KaiPereira/build-a-devboard/journal/Pasted image 20250828214635.png

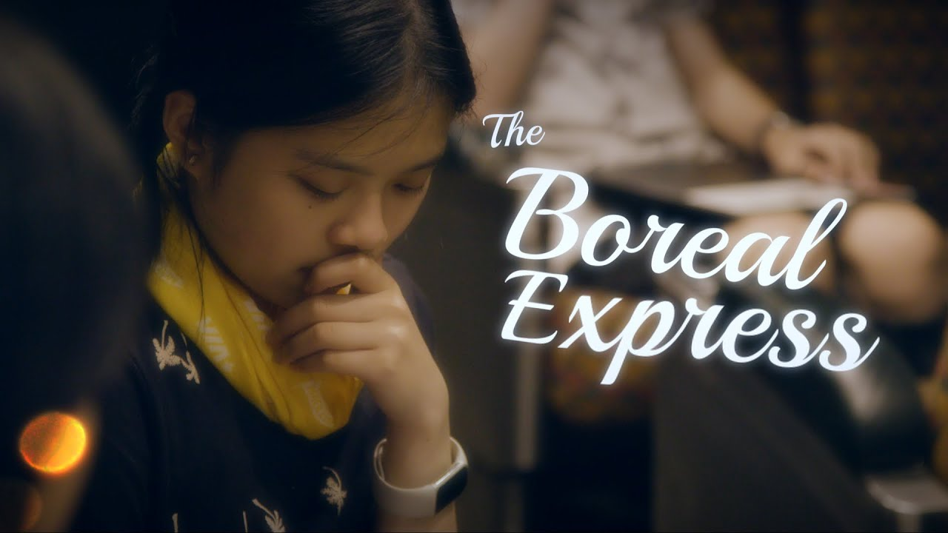
journal/Pasted image 20250828214635.png
