KaiPereira/build-a-devboard/journal/Pasted image 20250828221741.png

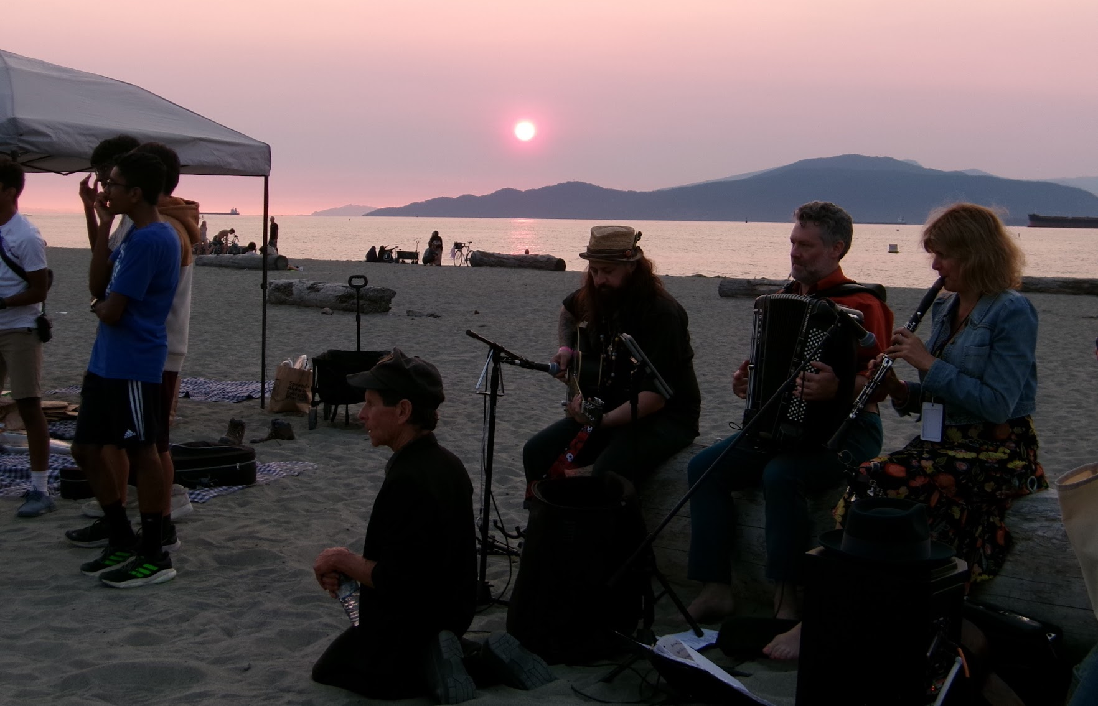
journal/Pasted image 20250828221741.png
