KaiPereira/build-a-devboard/journal/Pasted image 20250828224618.png

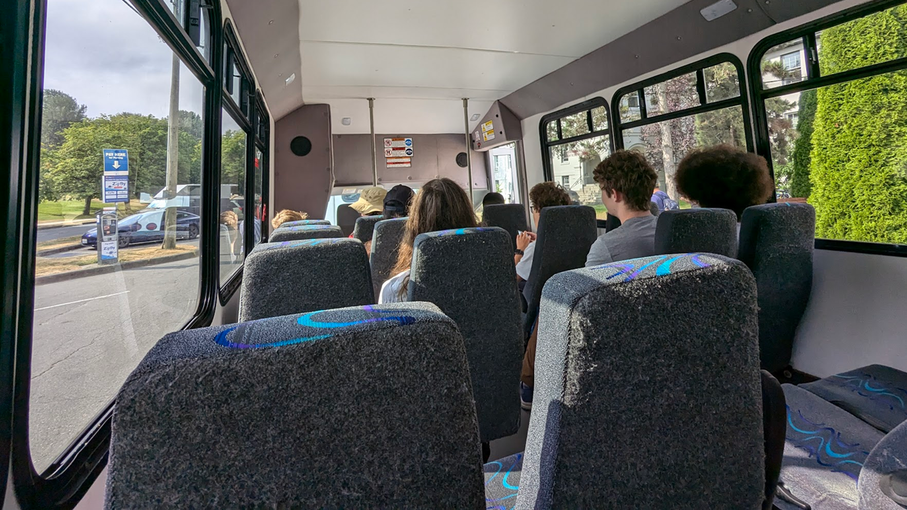
journal/Pasted image 20250828224618.png
