KaiPereira/build-a-devboard/journal/Pasted image 20250828224701.png

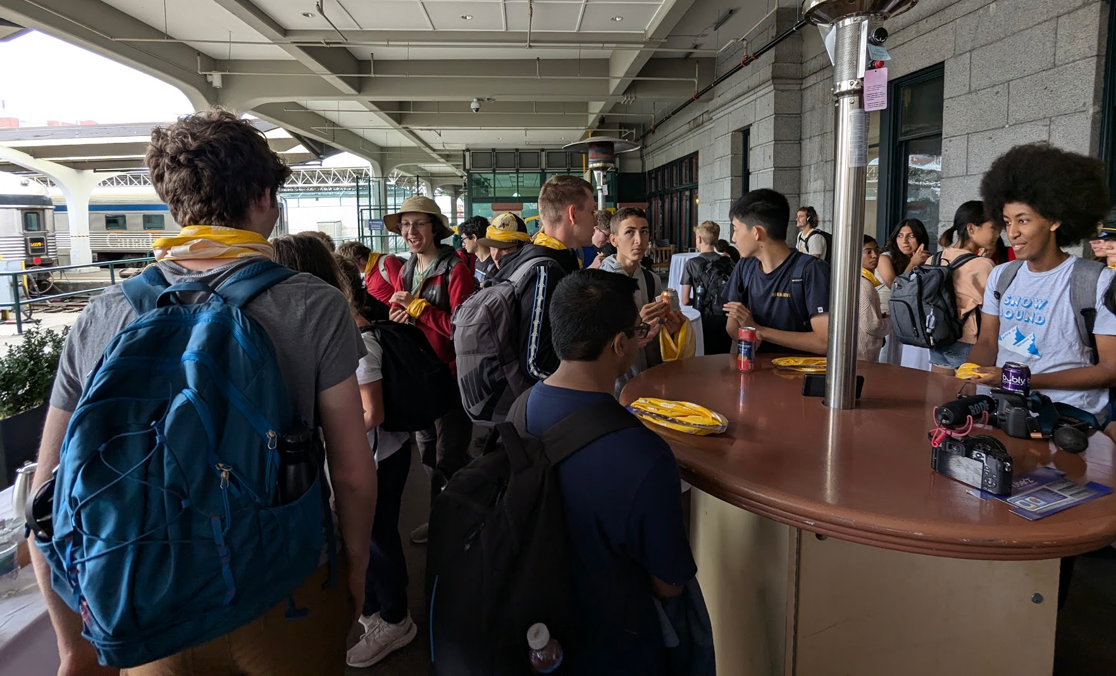
journal/Pasted image 20250828224701.png
