KaiPereira/build-a-devboard/journal/Pasted image 20250828225130.png

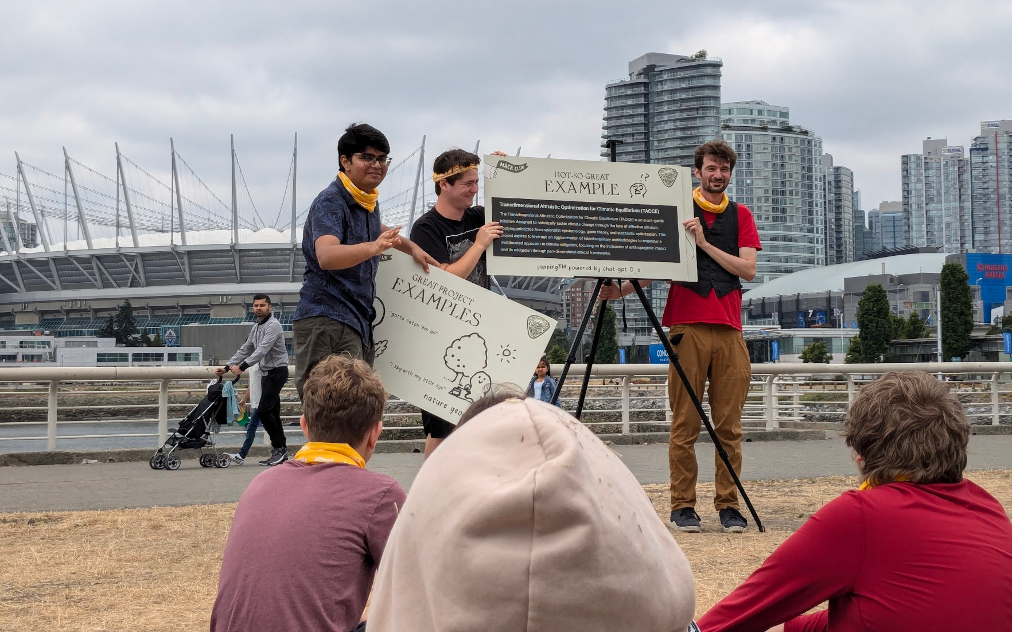
journal/Pasted image 20250828225130.png
