KaiPereira/build-a-devboard/journal/Pasted image 20250828225333.png

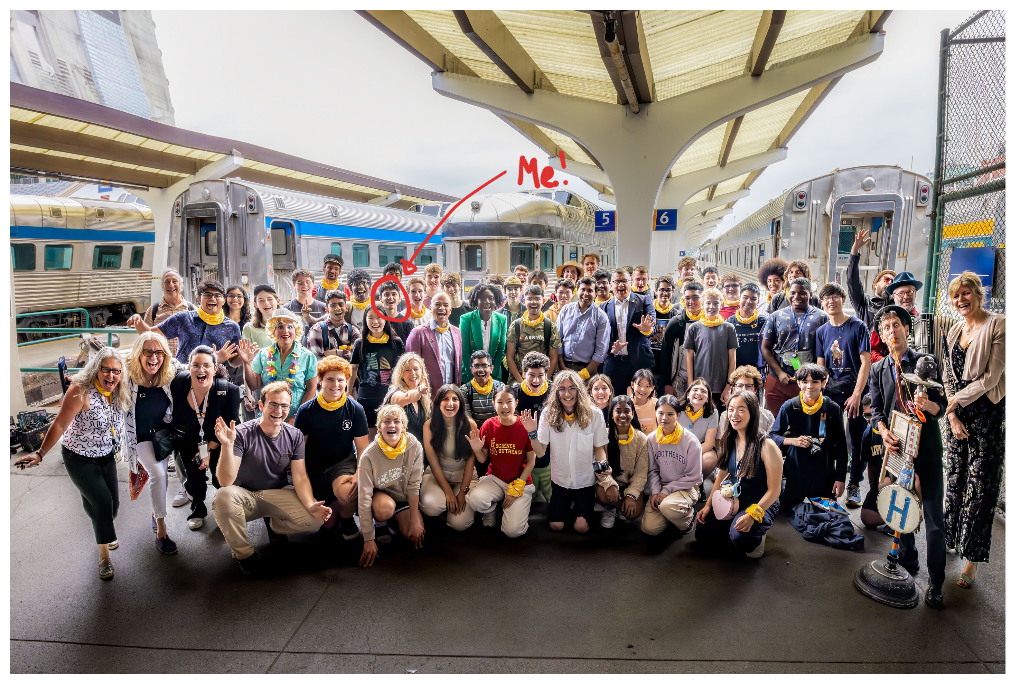
journal/Pasted image 20250828225333.png
