KaiPereira/build-a-devboard/journal/Pasted image 20250828225424.png

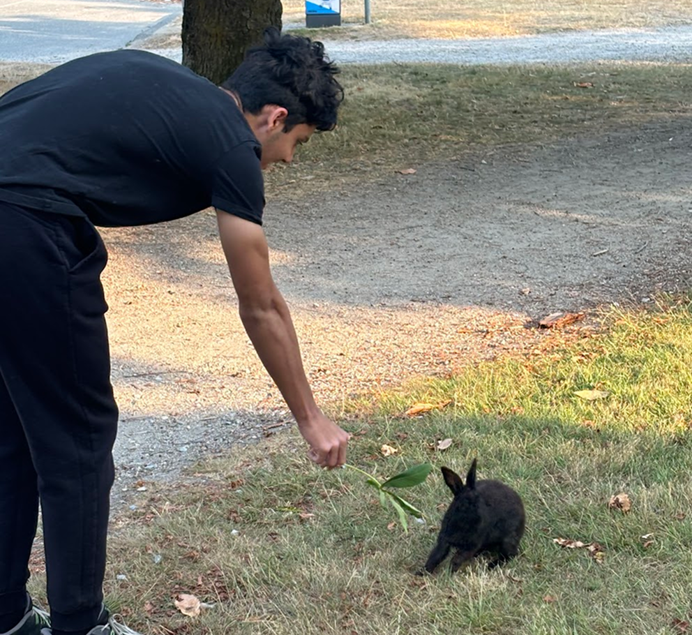
journal/Pasted image 20250828225424.png
