KaiPereira/build-a-devboard/journal/Pasted image 20250828230733.png

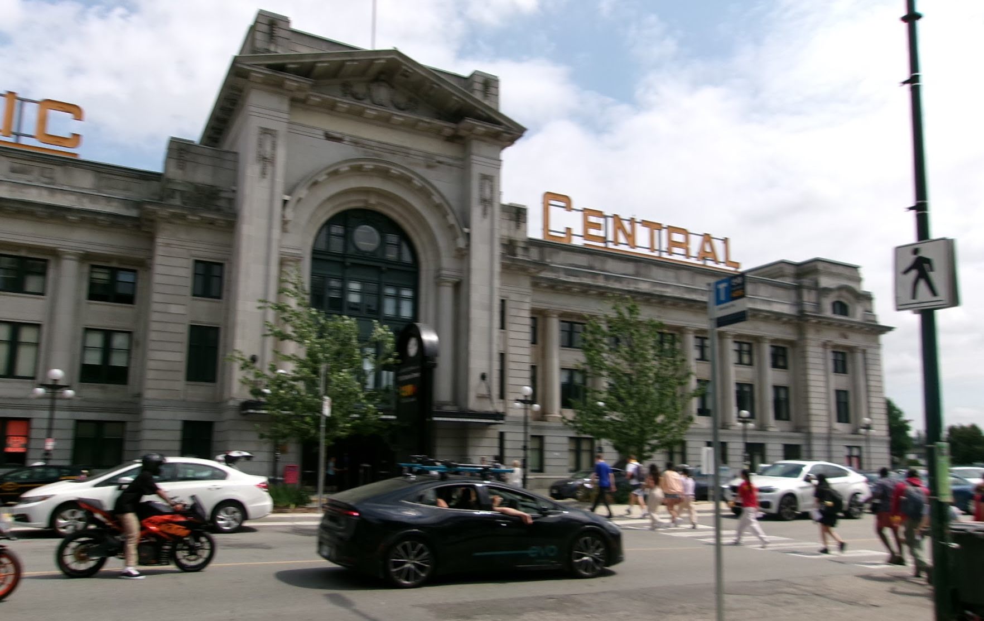
journal/Pasted image 20250828230733.png
