KaiPereira/build-a-devboard/journal/Pasted image 20250828233427.png

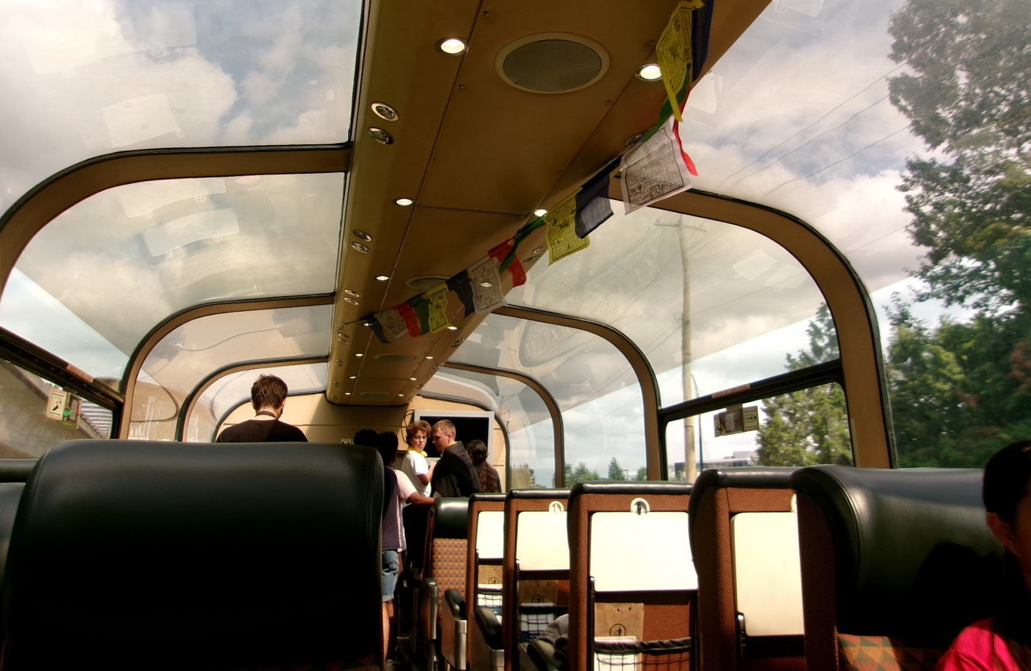
journal/Pasted image 20250828233427.png
