KaiPereira/build-a-devboard/journal/Pasted image 20250828234556.png

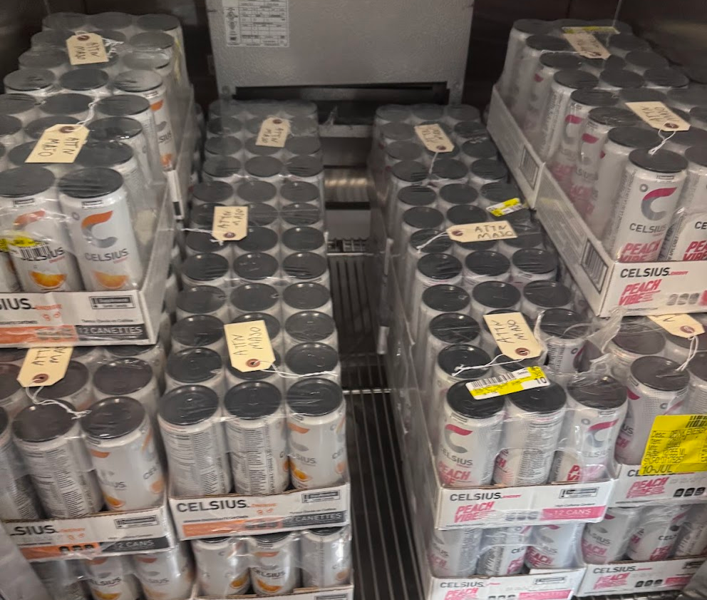
journal/Pasted image 20250828234556.png
