KaiPereira/build-a-devboard/journal/Pasted image 20250828234612.png

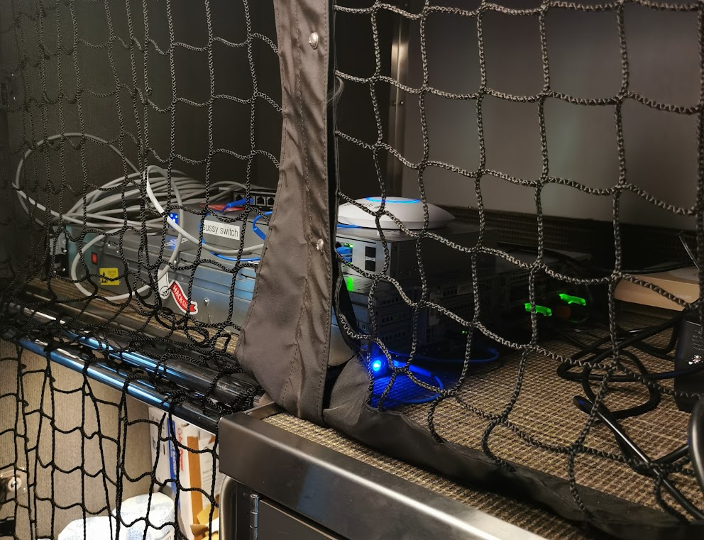
journal/Pasted image 20250828234612.png
