KaiPereira/build-a-devboard/journal/Pasted image 20250828234858.png

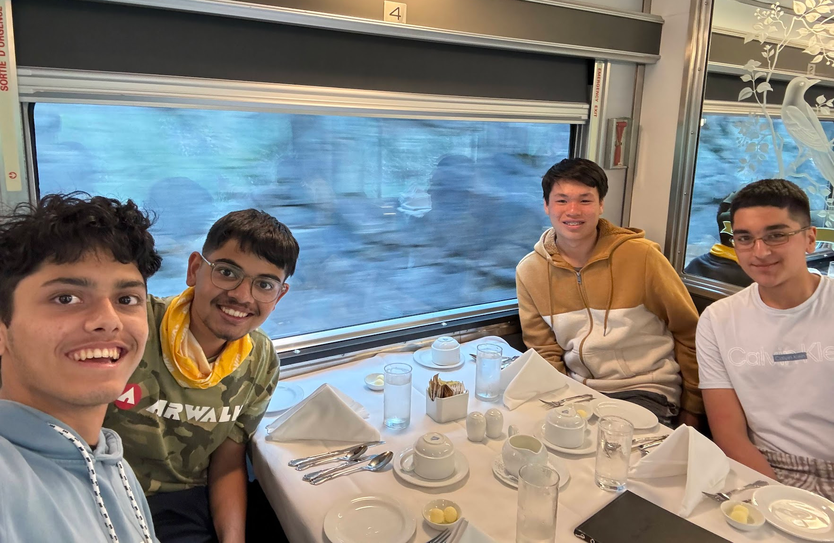
journal/Pasted image 20250828234858.png
