KaiPereira/build-a-devboard/journal/Pasted image 20250829002450.png

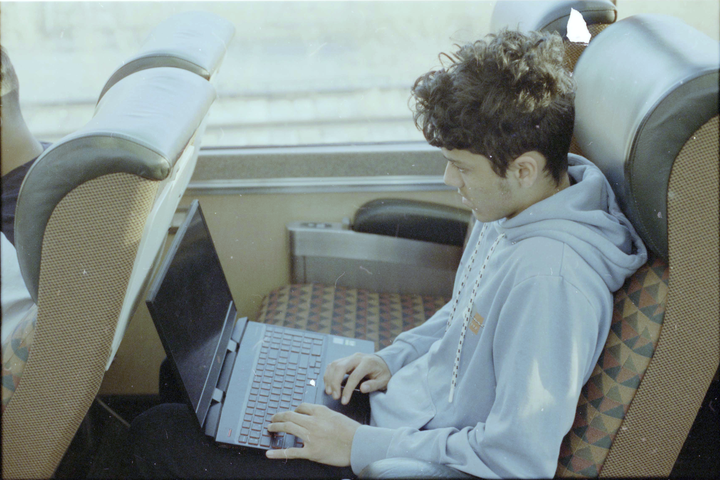
journal/Pasted image 20250829002450.png
