KaiPereira/build-a-devboard/journal/Pasted image 20250829003156.png

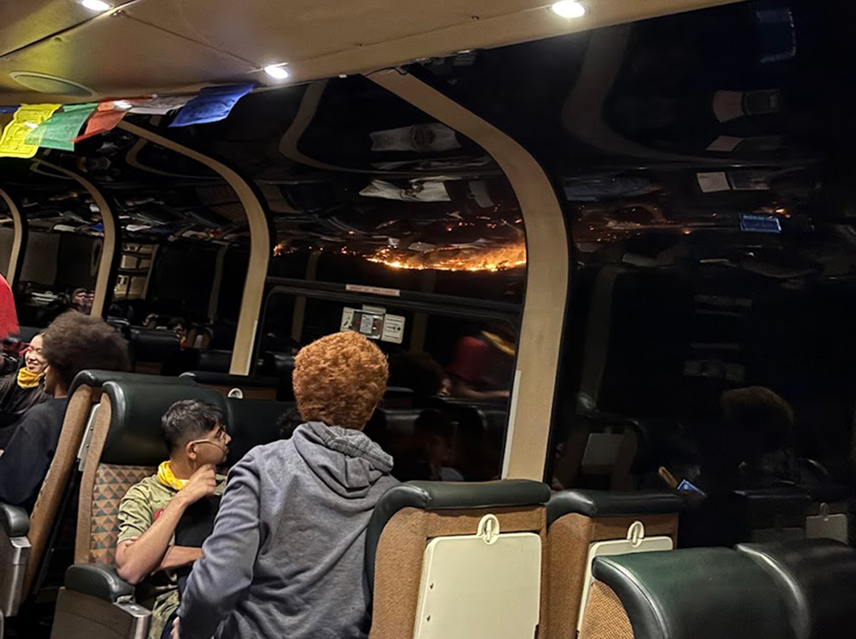
journal/Pasted image 20250829003156.png
