KaiPereira/build-a-devboard/journal/Pasted image 20250829004820.png

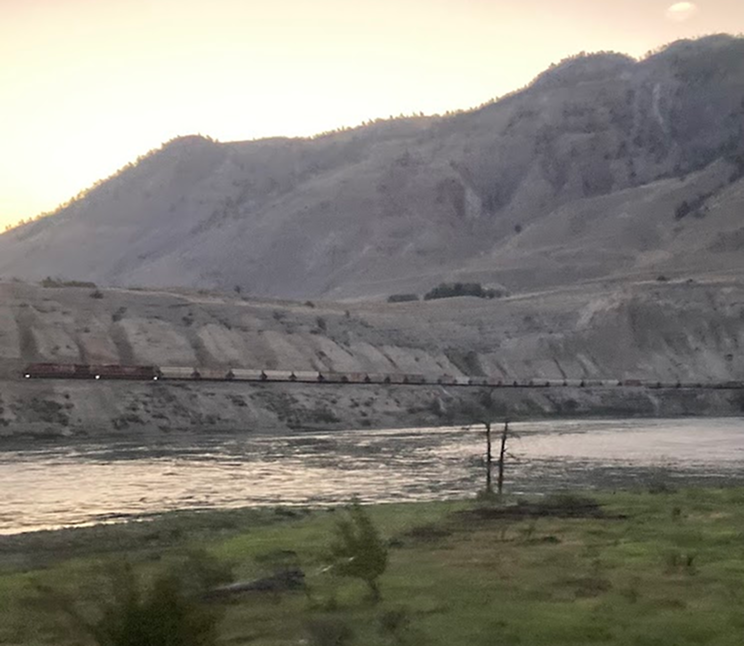
journal/Pasted image 20250829004820.png
