KaiPereira/build-a-devboard/journal/Pasted image 20250829005805.png

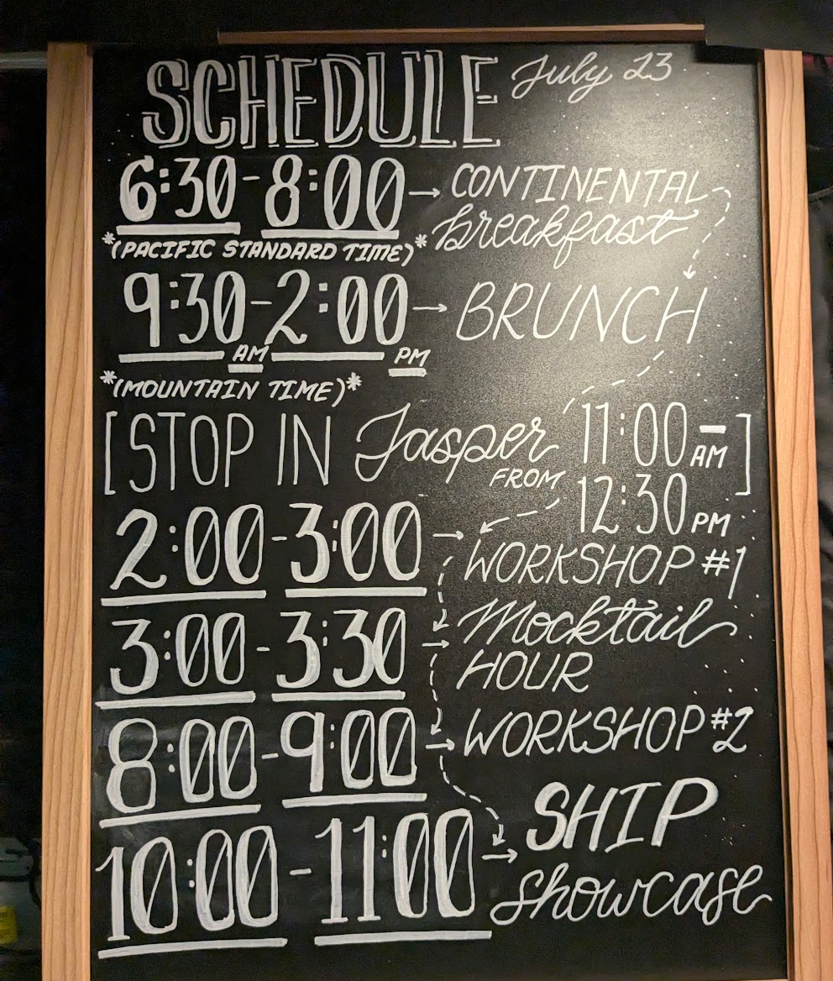
journal/Pasted image 20250829005805.png
