KaiPereira/build-a-devboard/journal/Pasted image 20250829161614.png

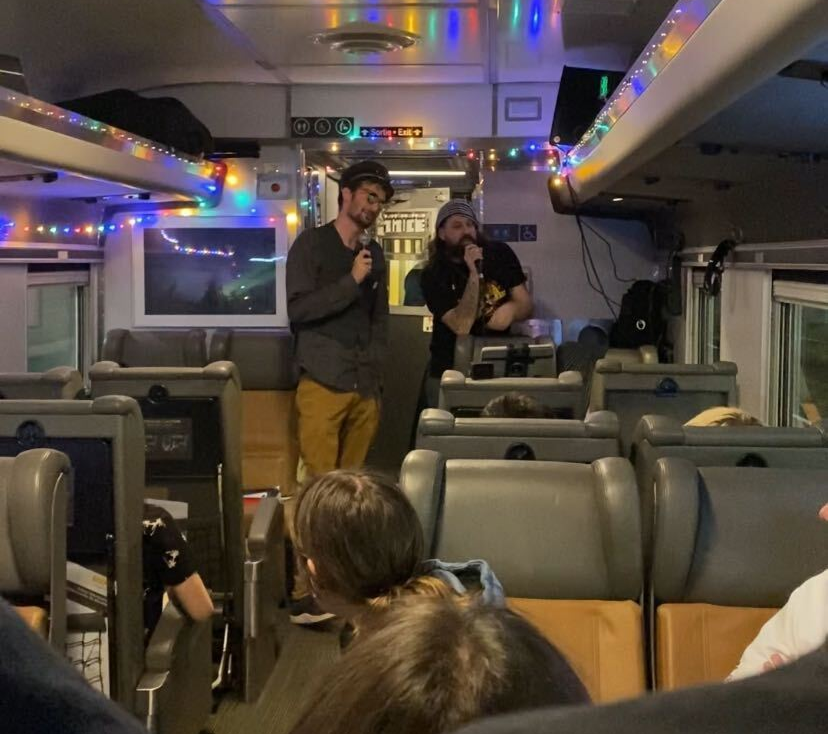
journal/Pasted image 20250829161614.png
