KaiPereira/build-a-devboard/journal/Pasted image 20250829162045.png

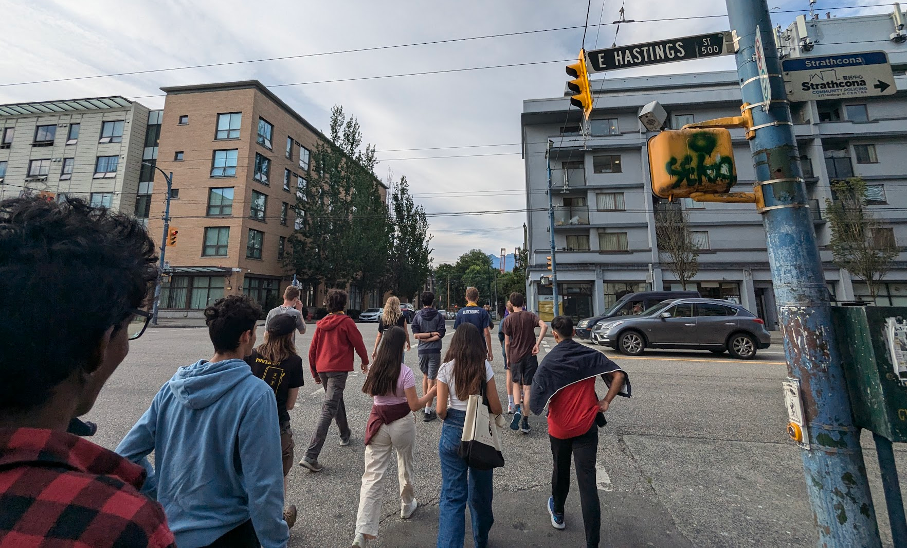
journal/Pasted image 20250829162045.png
