KaiPereira/build-a-devboard/journal/Pasted image 20250829164850.png

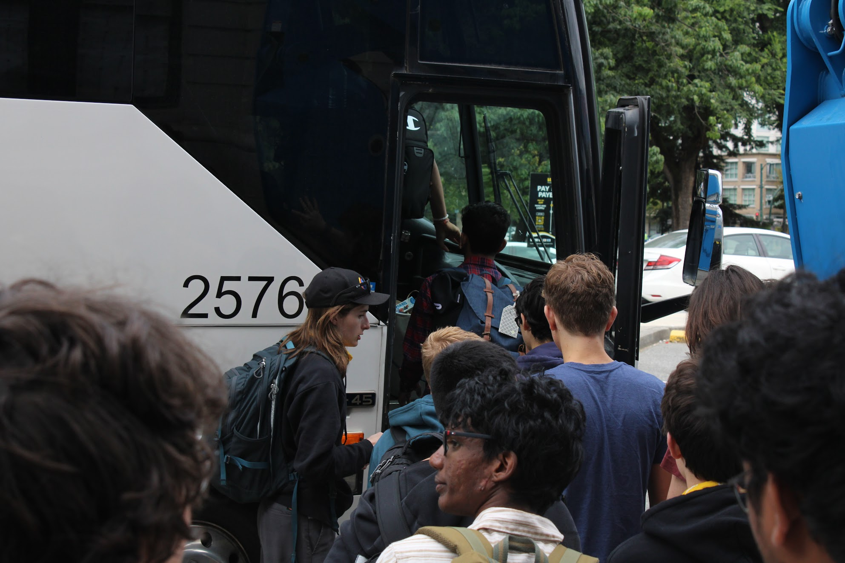
journal/Pasted image 20250829164850.png
