KaiPereira/build-a-devboard/journal/Pasted image 20250829165105.png

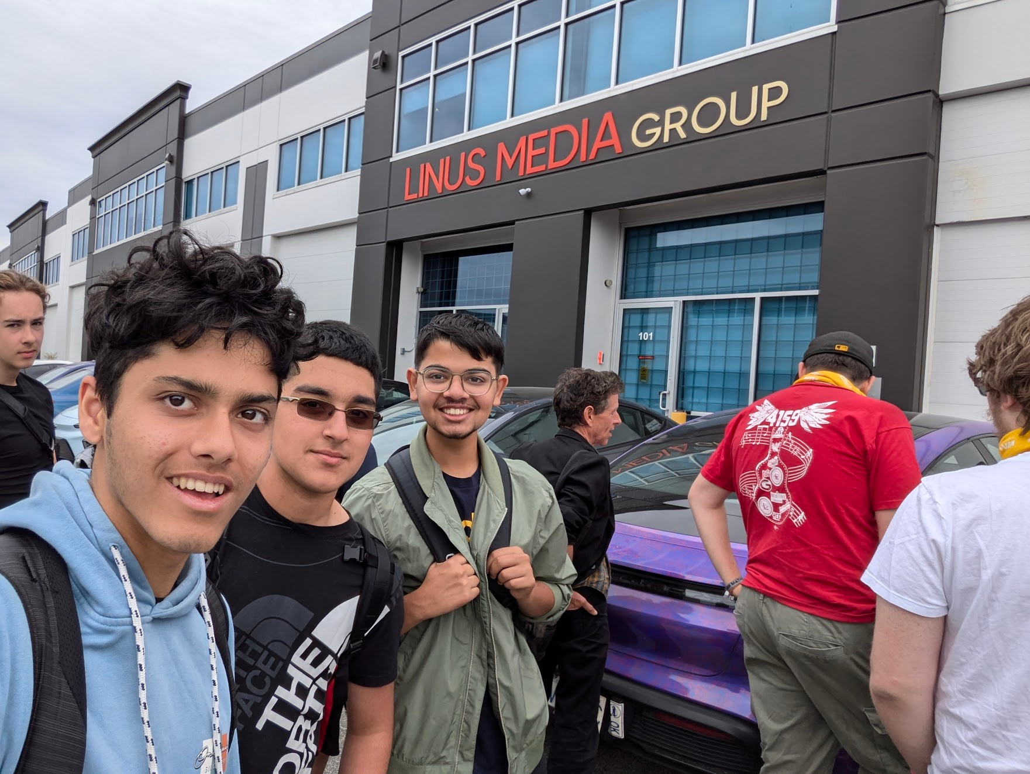
journal/Pasted image 20250829165105.png
