KaiPereira/build-a-devboard/journal/Pasted image 20250829165130.png

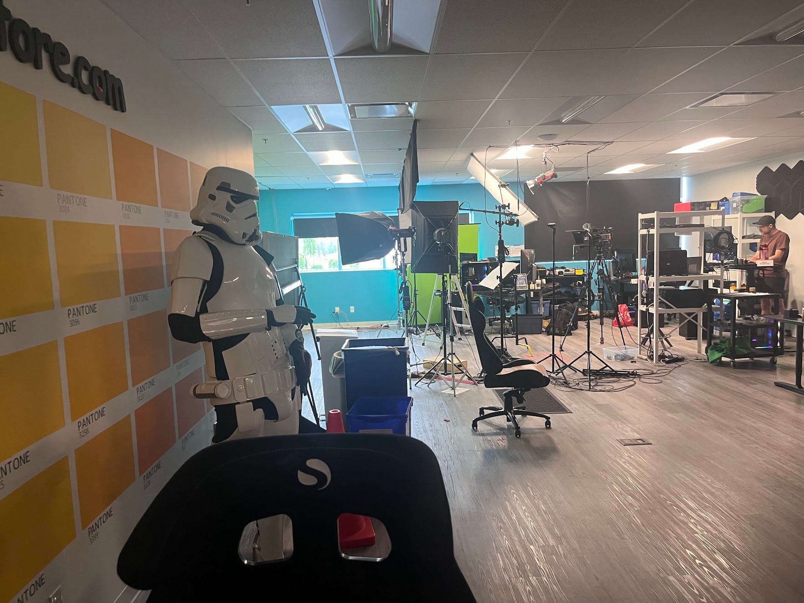
journal/Pasted image 20250829165130.png
