KaiPereira/build-a-devboard/journal/Pasted image 20250829165152.png

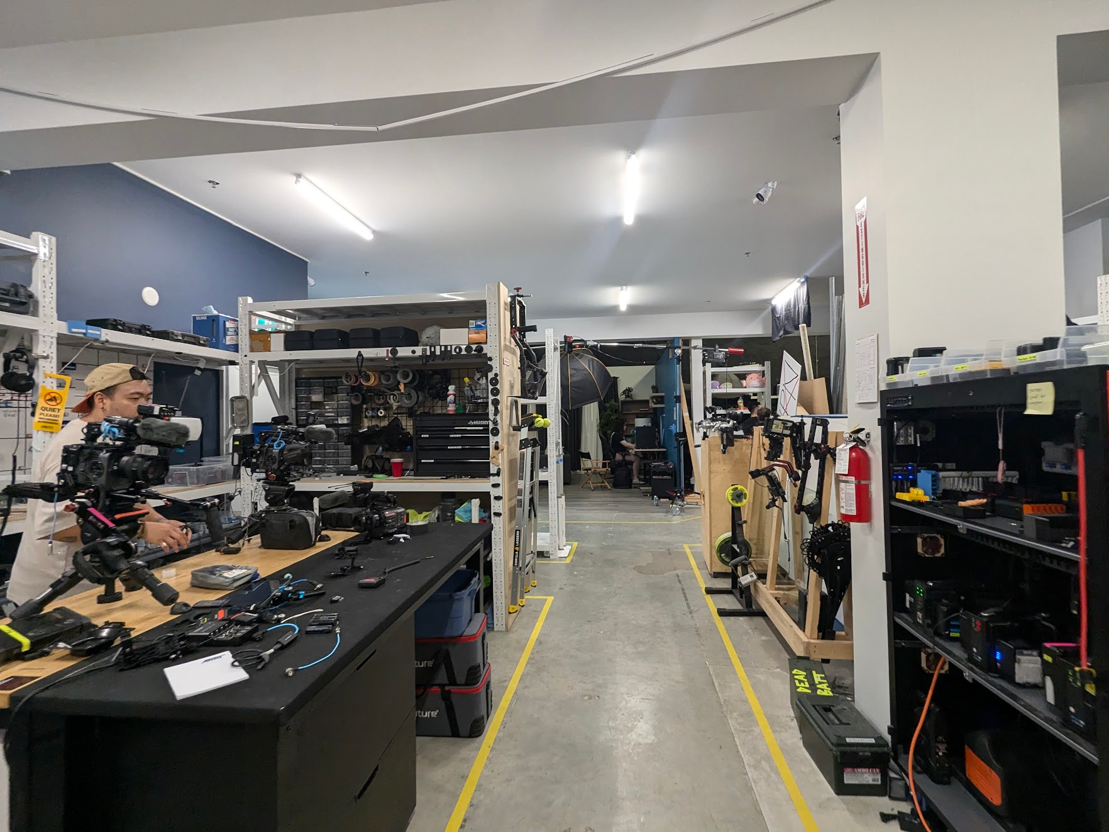
journal/Pasted image 20250829165152.png
