KaiPereira/build-a-devboard/journal/Pasted image 20250829165215.png

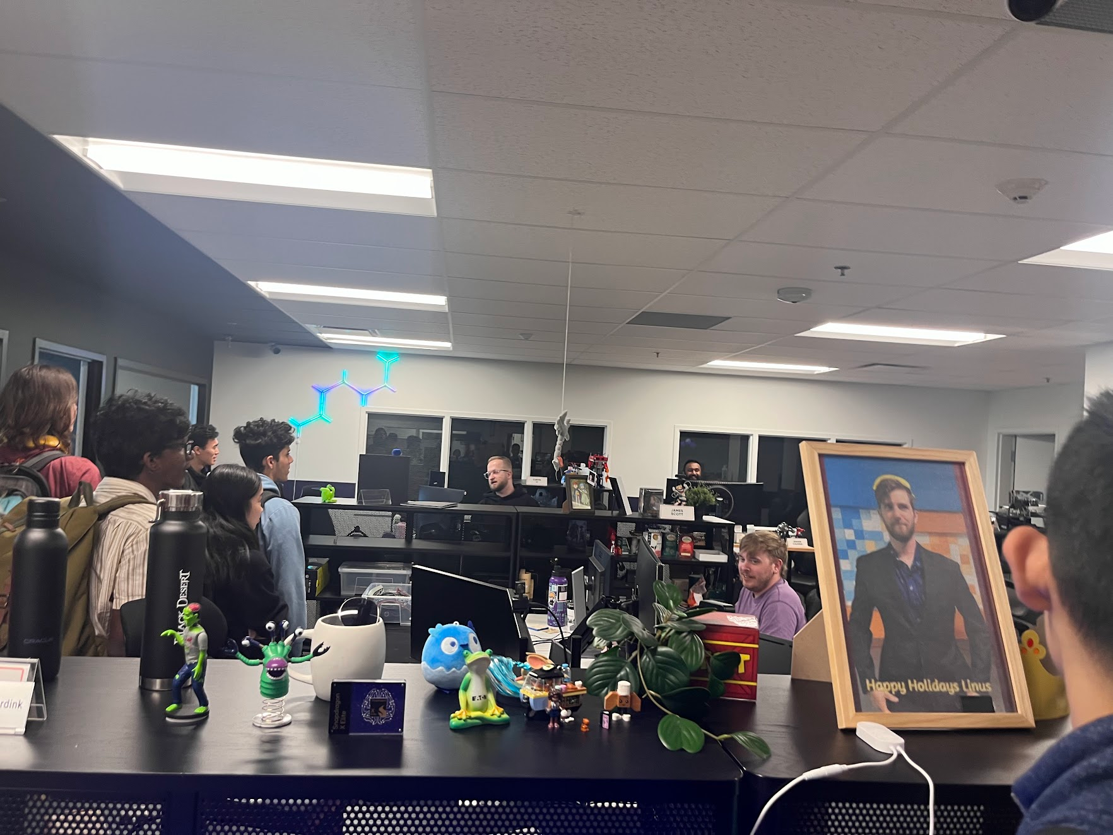
journal/Pasted image 20250829165215.png
