KaiPereira/build-a-devboard/journal/Pasted image 20250829165408.png

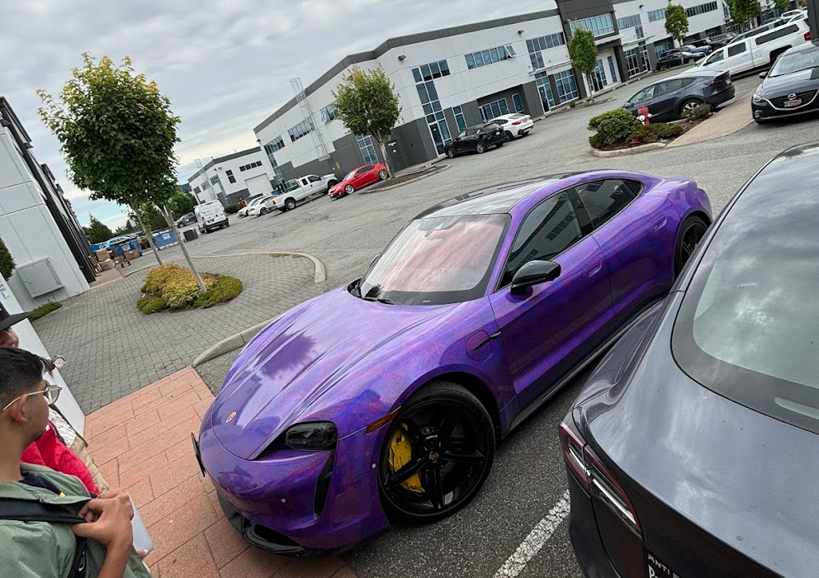
journal/Pasted image 20250829165408.png
