KaiPereira/build-a-devboard/journal/Pasted image 20250829182641.png

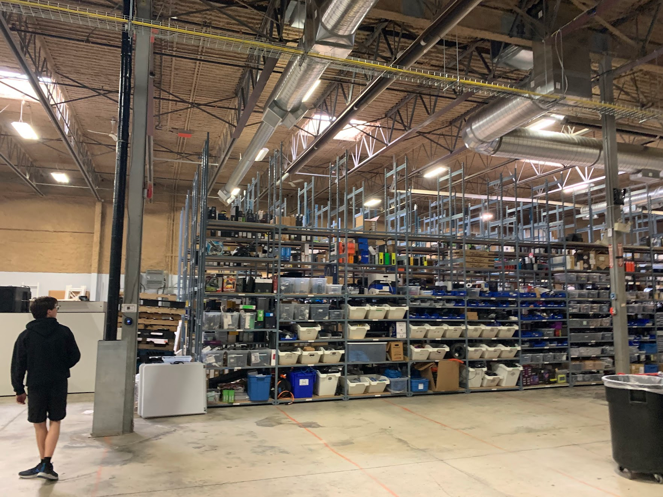
journal/Pasted image 20250829182641.png
