KaiPereira/build-a-devboard/journal/Pasted image 20250925070807.png

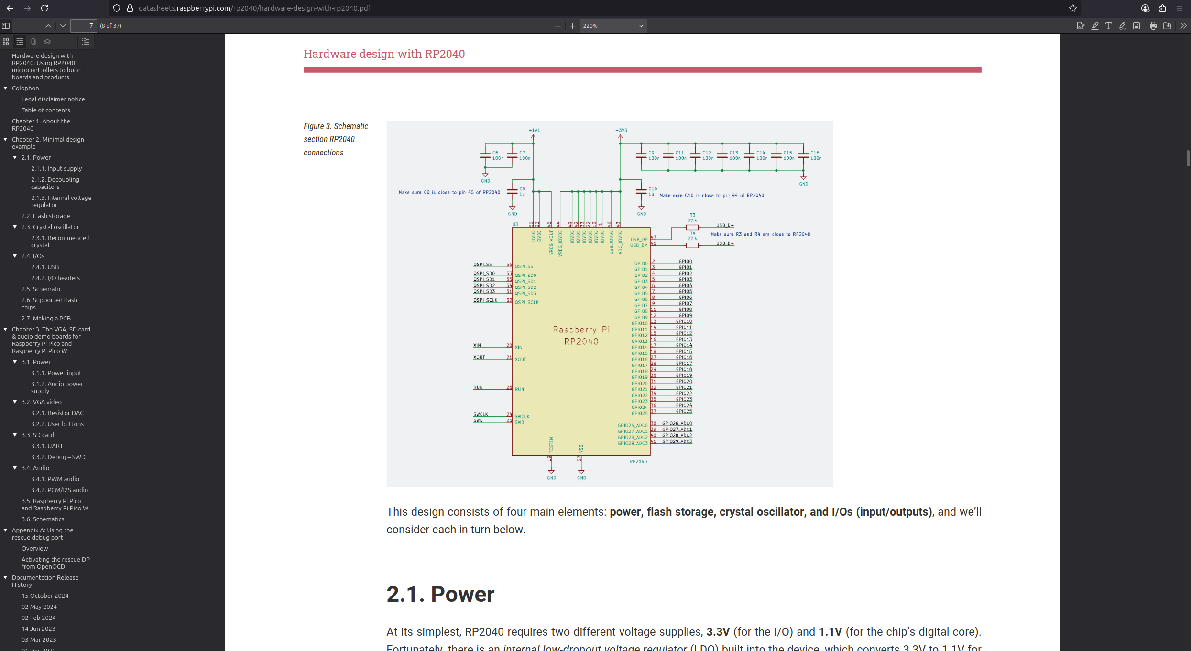
journal/Pasted image 20250925070807.png
