KaiPereira/build-a-devboard/journal/Pasted image 20250925160300.png

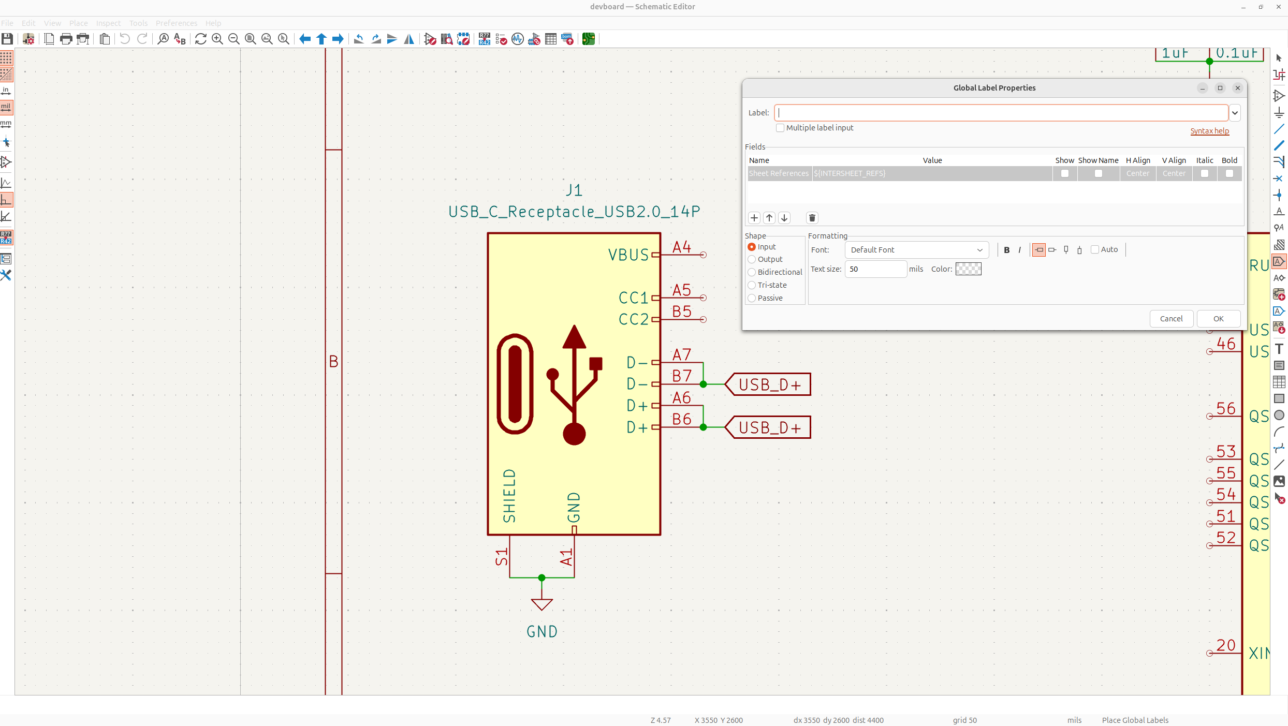
journal/Pasted image 20250925160300.png
