KaiPereira/build-a-devboard/journal/Pasted image 20250925160549.png

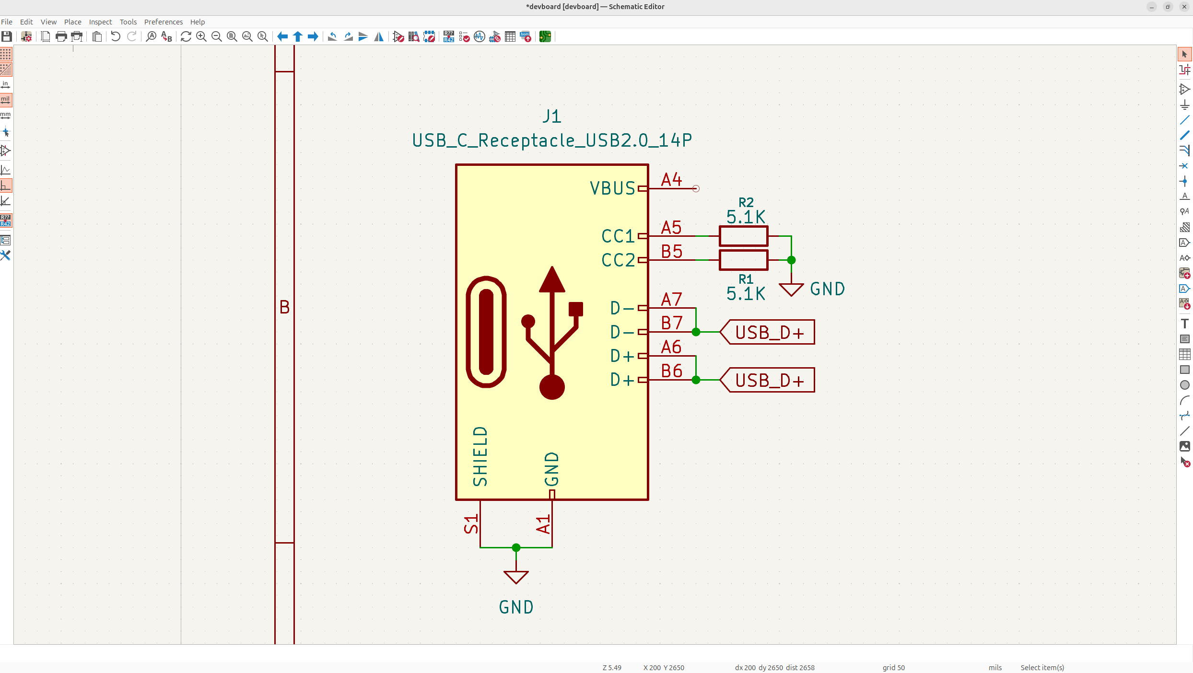
journal/Pasted image 20250925160549.png
