KaiPereira/build-a-devboard/journal/Pasted image 20250925161539.png

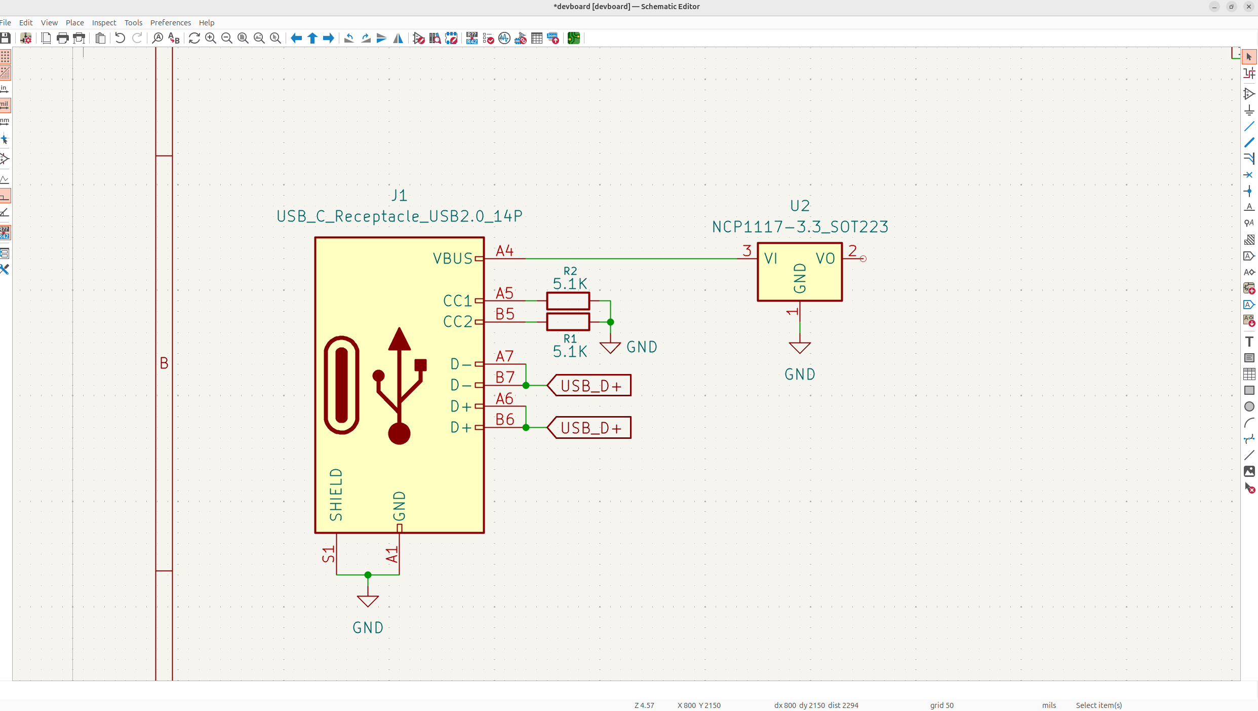
journal/Pasted image 20250925161539.png
