KaiPereira/build-a-devboard/journal/Pasted image 20250925161945.png

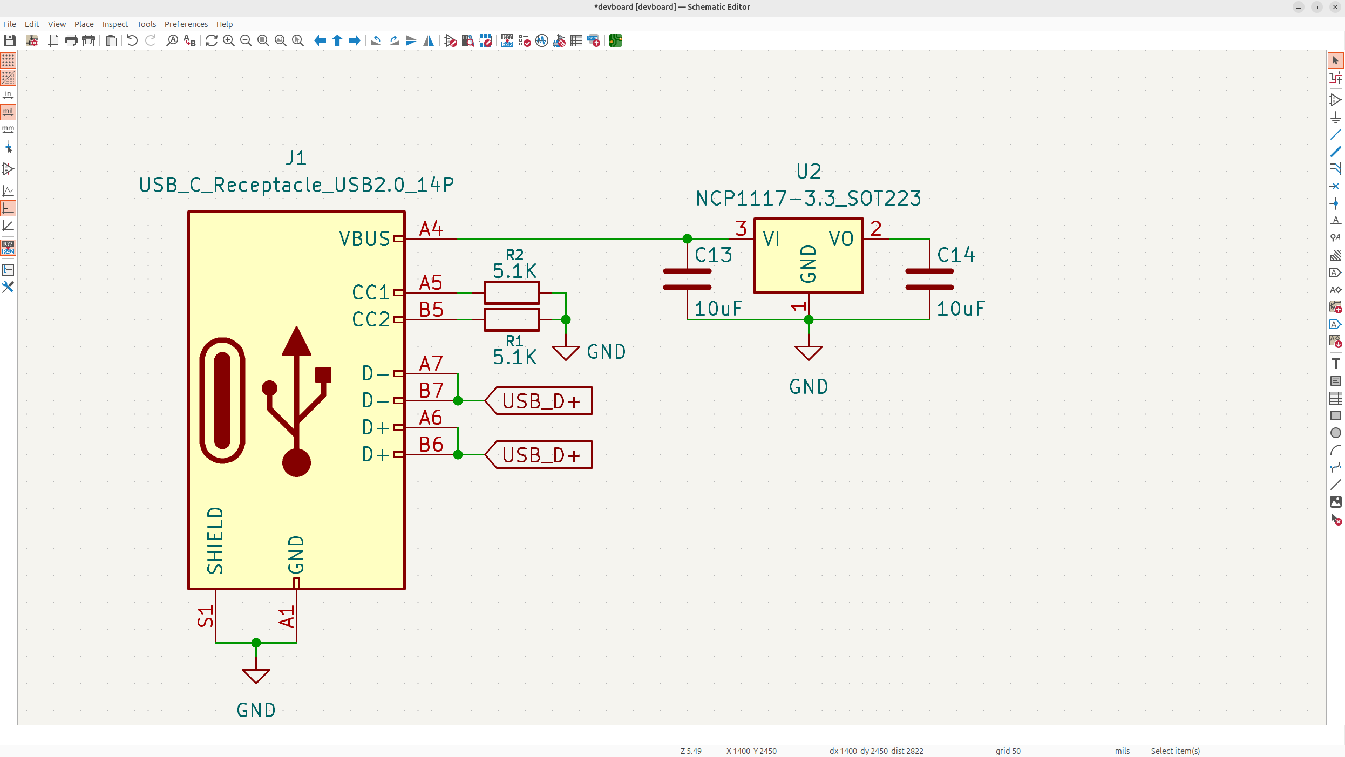
journal/Pasted image 20250925161945.png
