KaiPereira/build-a-devboard/journal/Pasted image 20250925162329.png

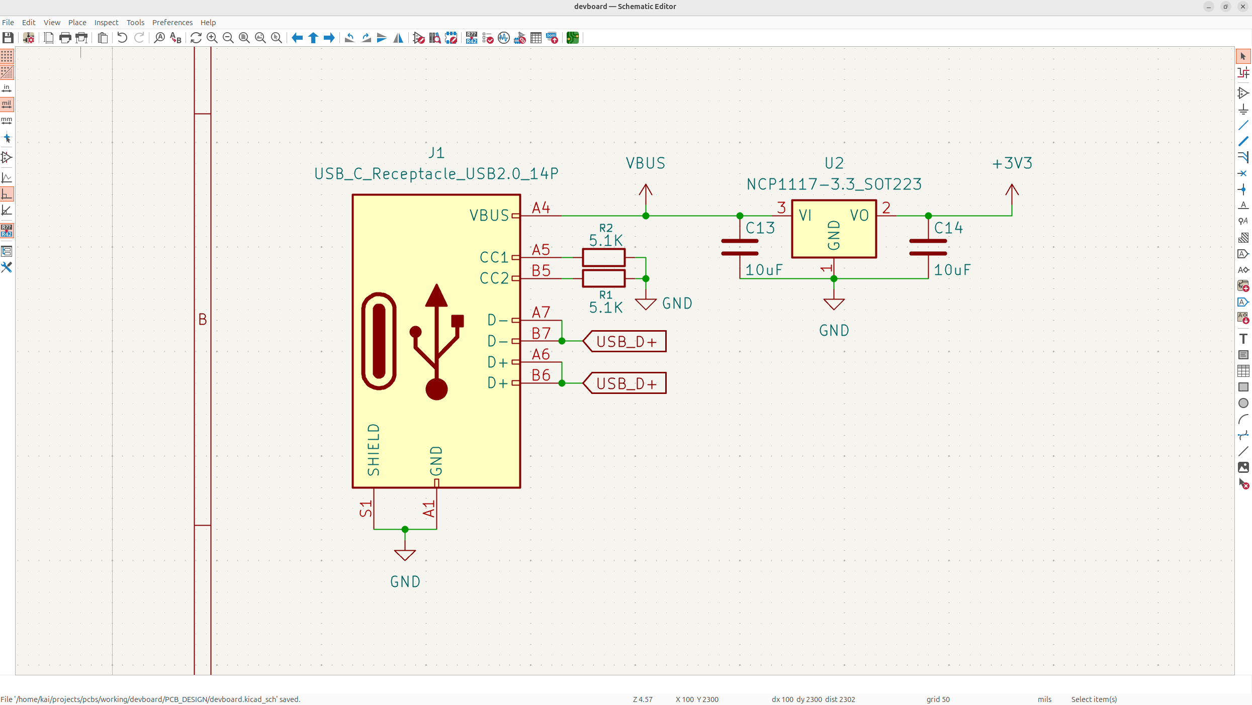
journal/Pasted image 20250925162329.png
