KaiPereira/build-a-devboard/journal/Pasted image 20250927190151.png

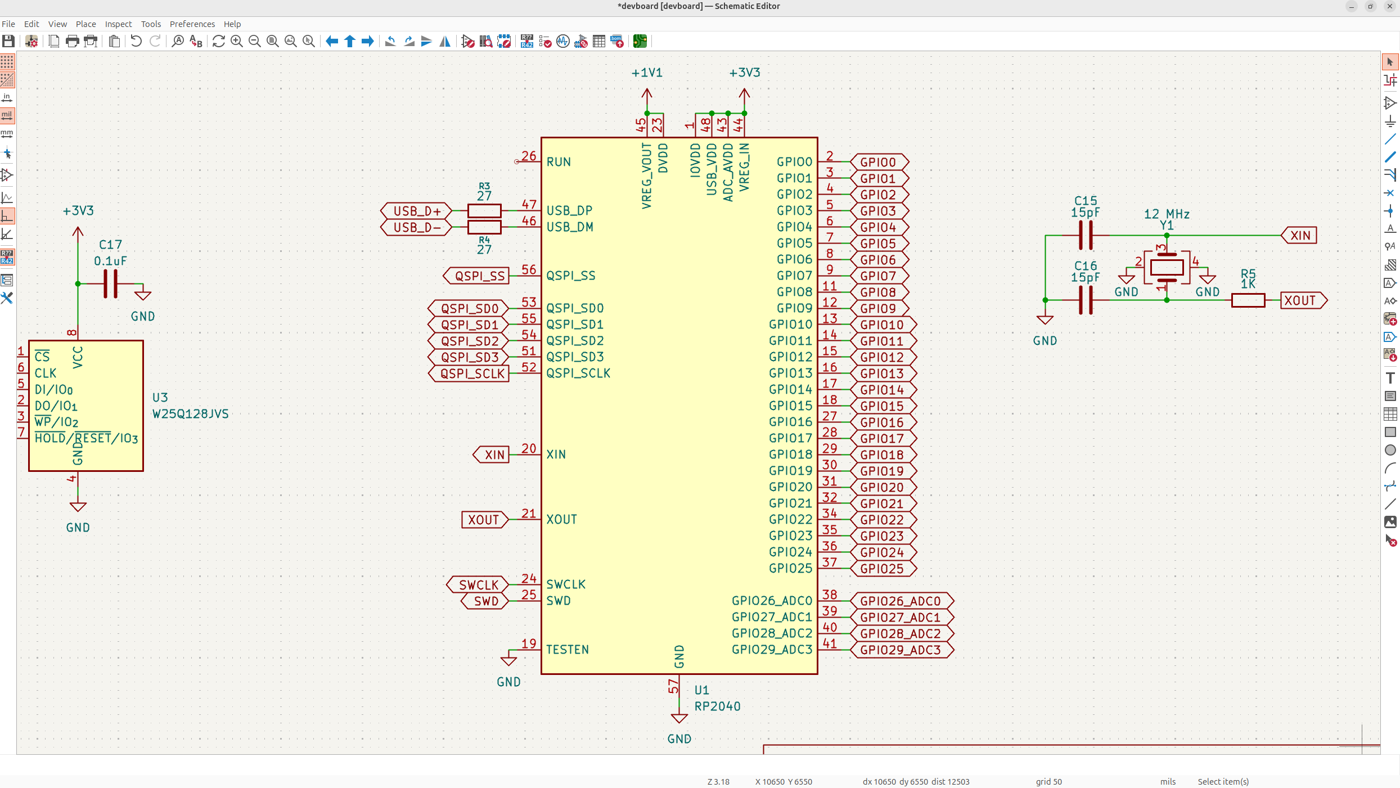
journal/Pasted image 20250927190151.png
