KaiPereira/build-a-devboard/journal/Pasted image 20250927190319.png

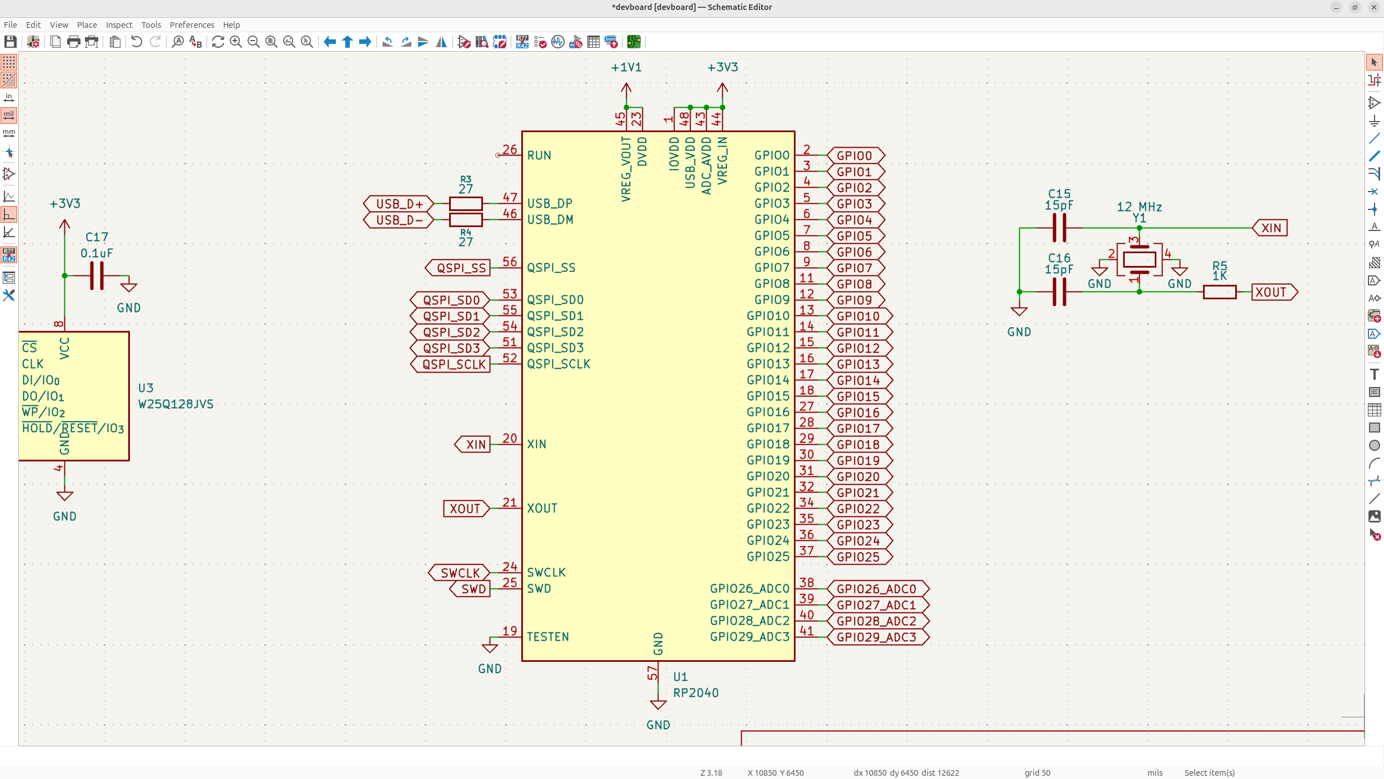
journal/Pasted image 20250927190319.png
