KaiPereira/build-a-devboard/journal/Pasted image 20250928011307.png

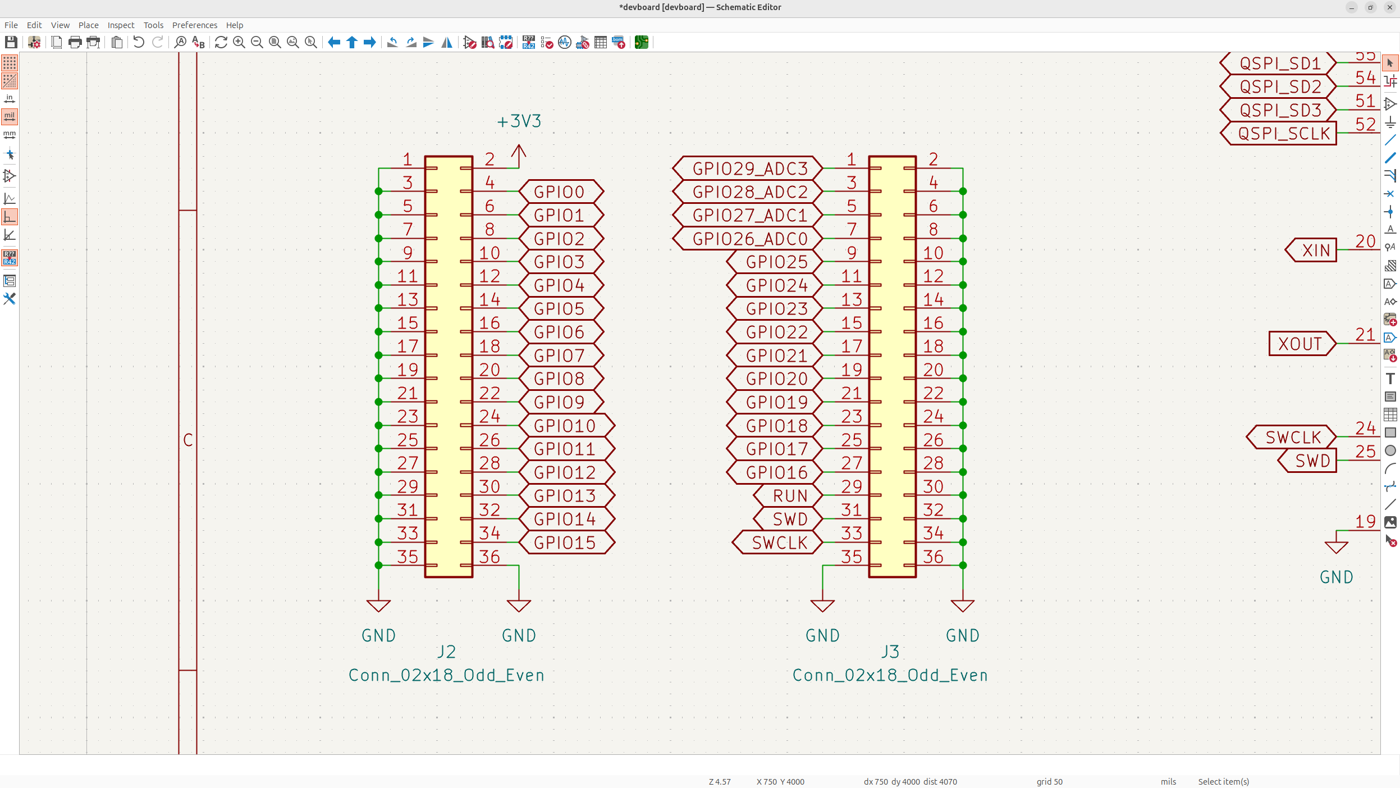
journal/Pasted image 20250928011307.png
