KaiPereira/build-a-devboard/journal/Pasted image 20250928011353.png

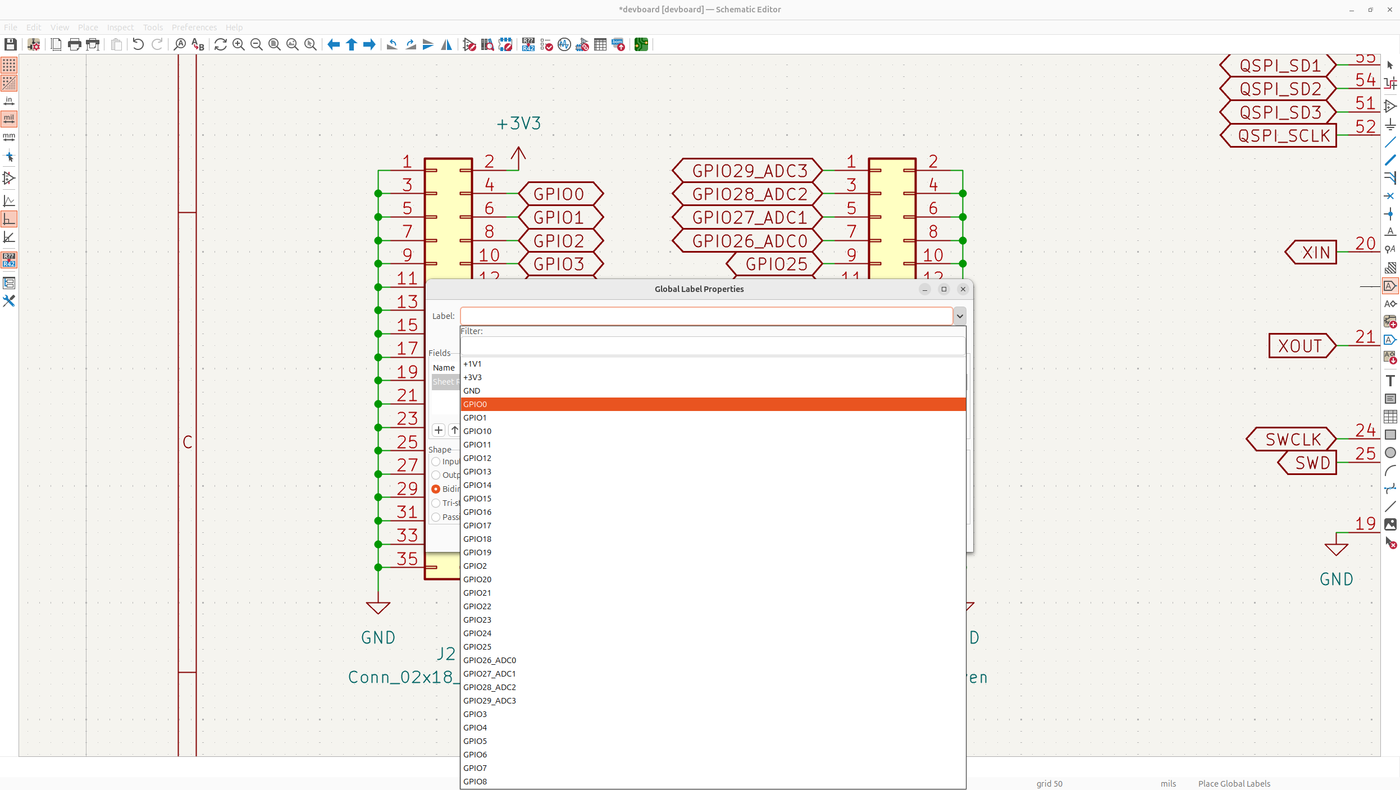
journal/Pasted image 20250928011353.png
