KaiPereira/build-a-devboard/journal/Pasted image 20250928011553.png

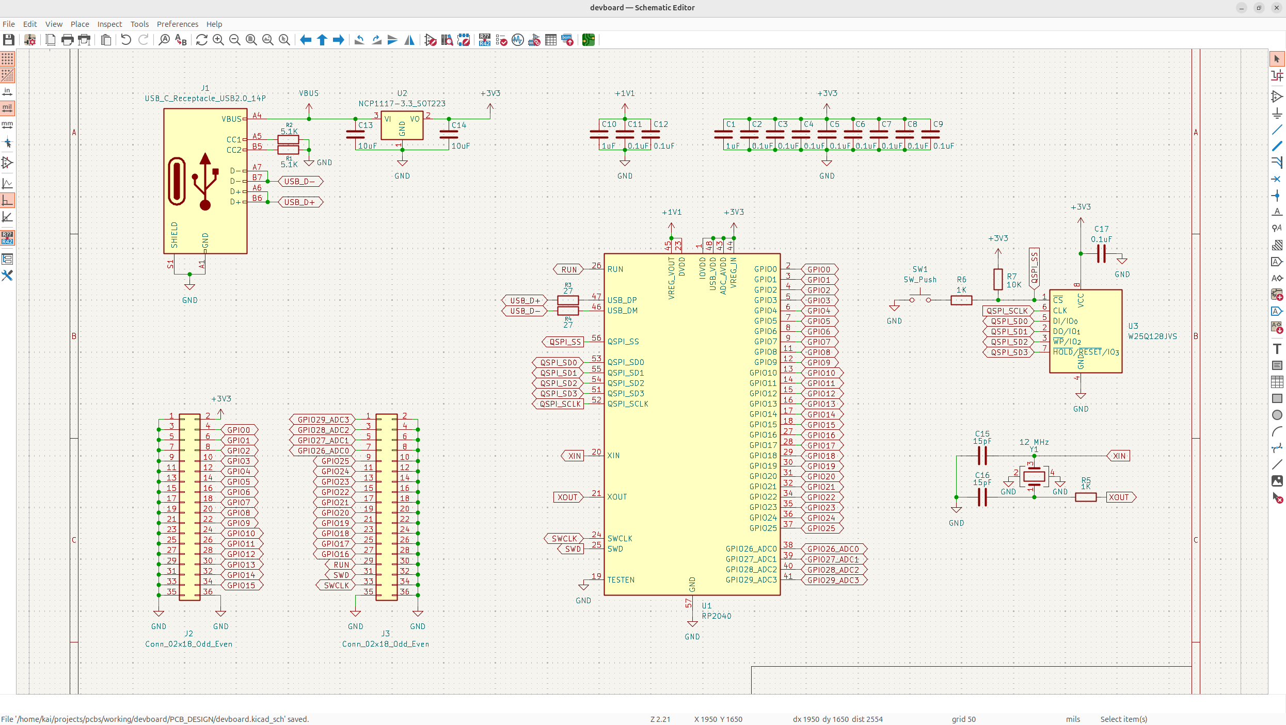
journal/Pasted image 20250928011553.png
