KaiPereira/build-a-devboard/journal/Pasted image 20250928012357.png

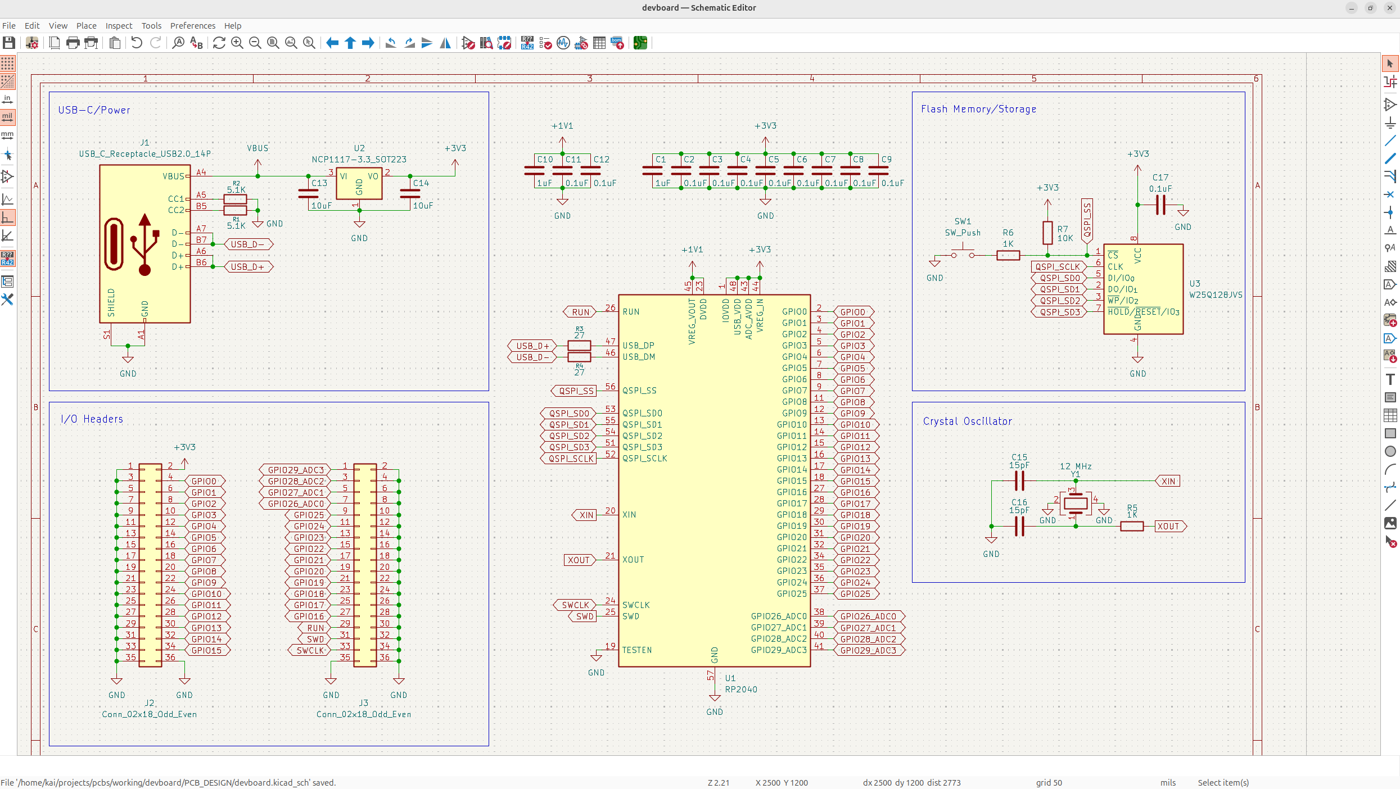
journal/Pasted image 20250928012357.png
