KaiPereira/build-a-devboard/journal/Pasted image 20250928012841.png

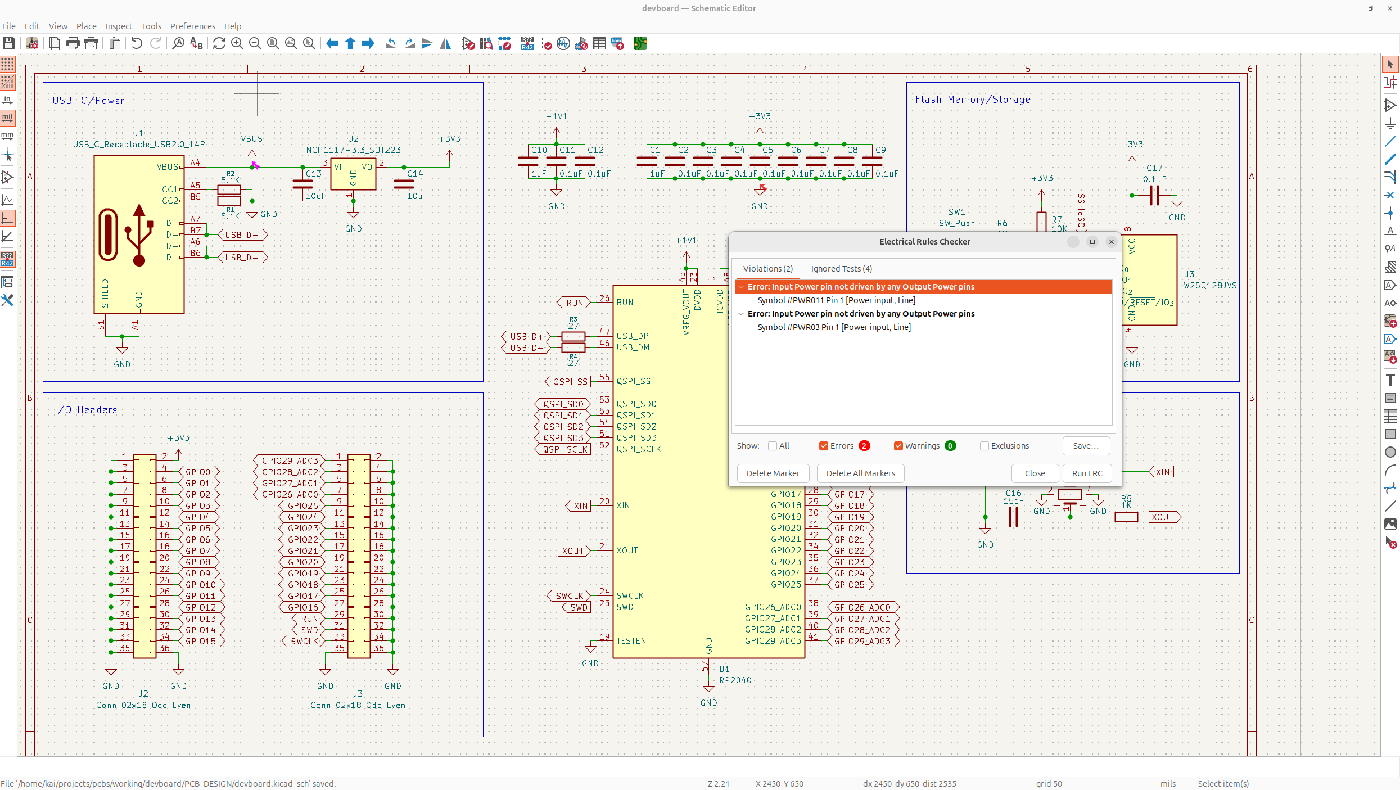
journal/Pasted image 20250928012841.png
