KaiPereira/build-a-devboard/journal/Pasted image 20250928014533.png

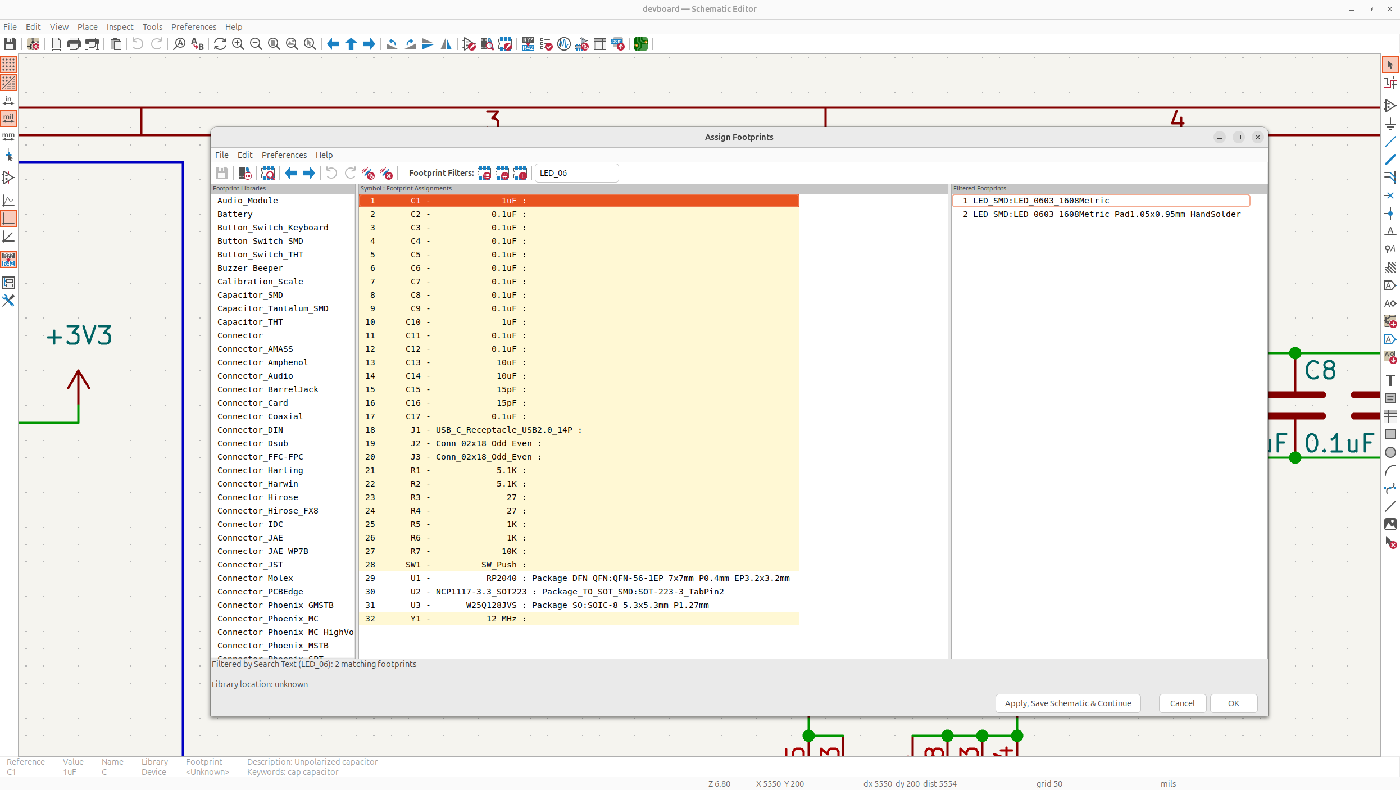
journal/Pasted image 20250928014533.png
