KaiPereira/build-a-devboard/journal/Pasted image 20250928015615.png

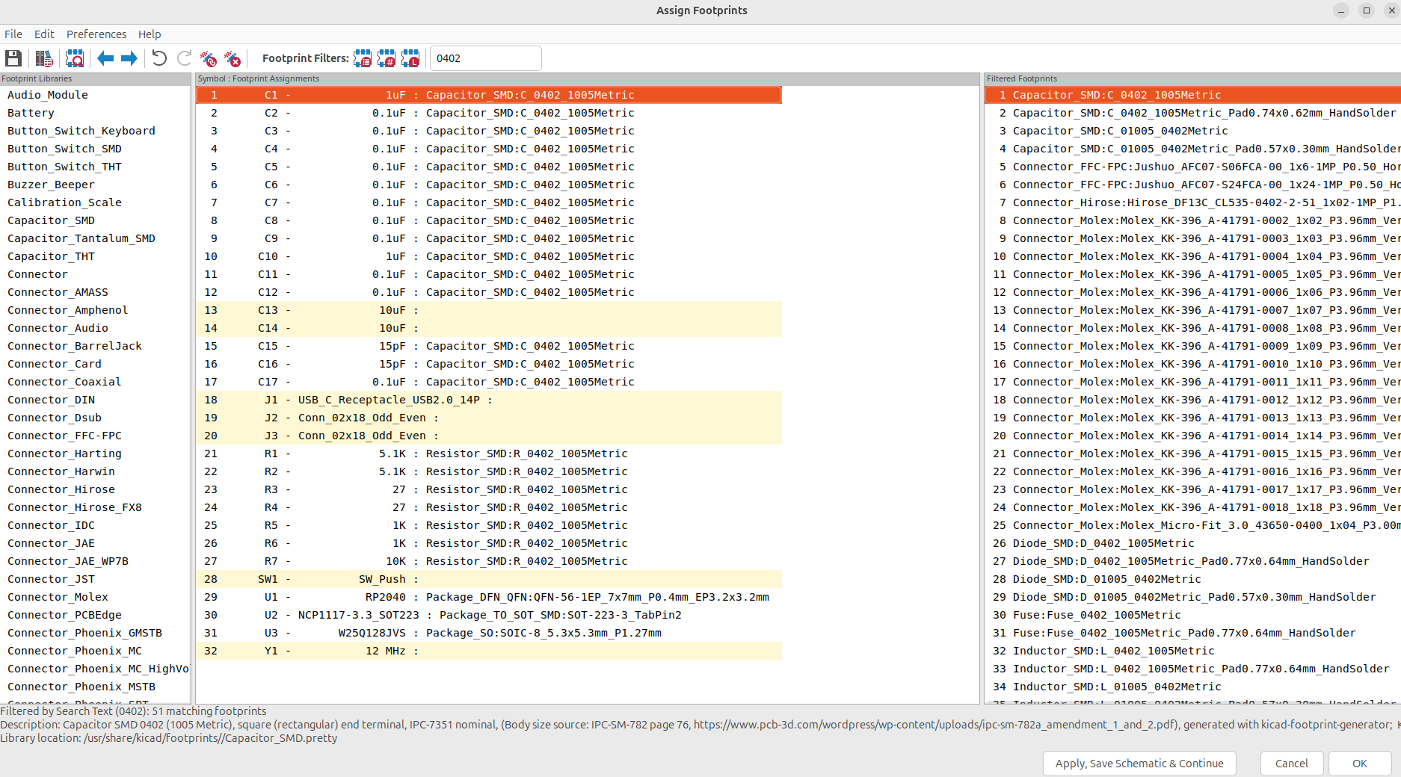
journal/Pasted image 20250928015615.png
