KaiPereira/build-a-devboard/journal/Pasted image 20250928015701.png

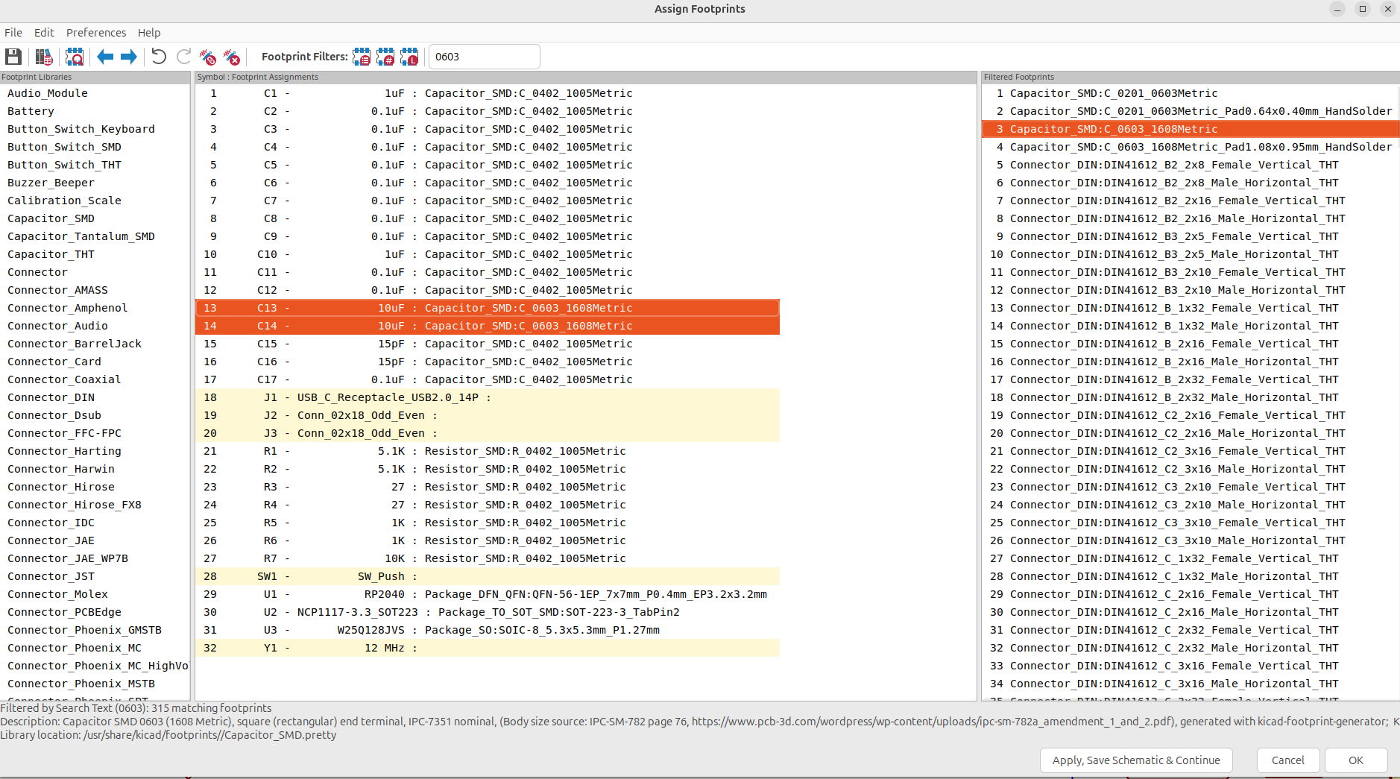
journal/Pasted image 20250928015701.png
