KaiPereira/build-a-devboard/journal/Pasted image 20250928210229.png

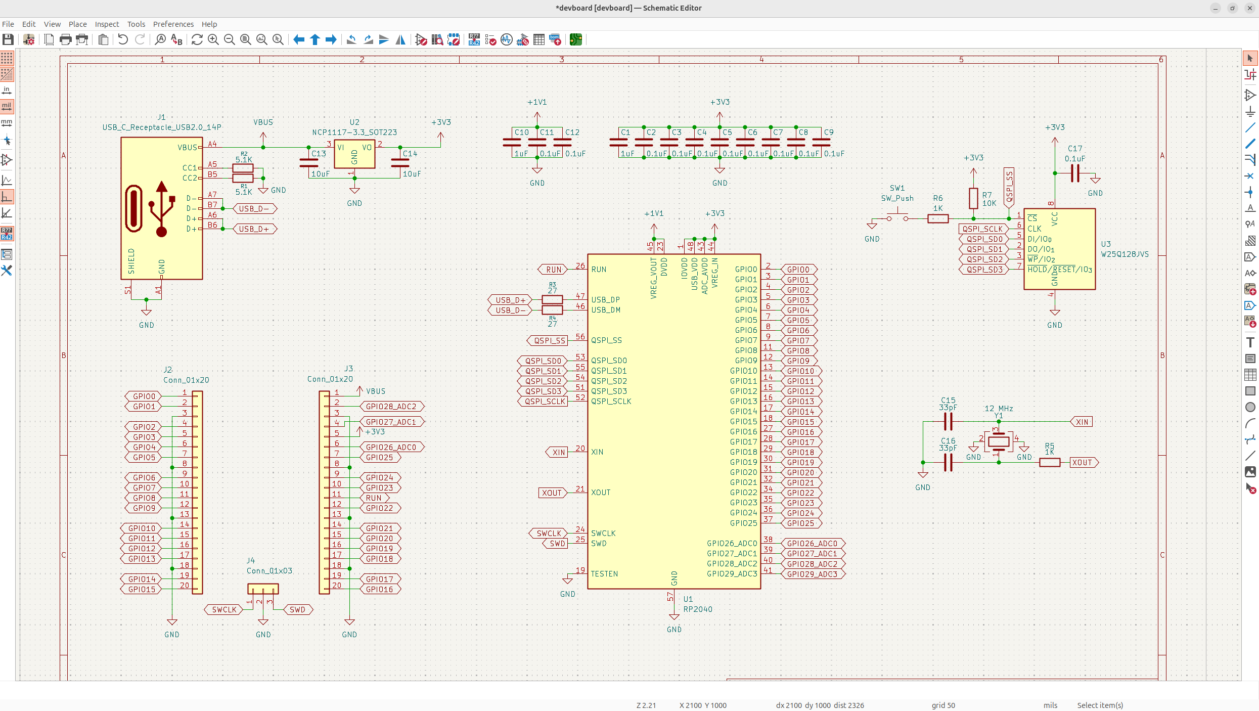
journal/Pasted image 20250928210229.png
