KaiPereira/build-a-devboard/journal/Pasted image 20250928215223.png

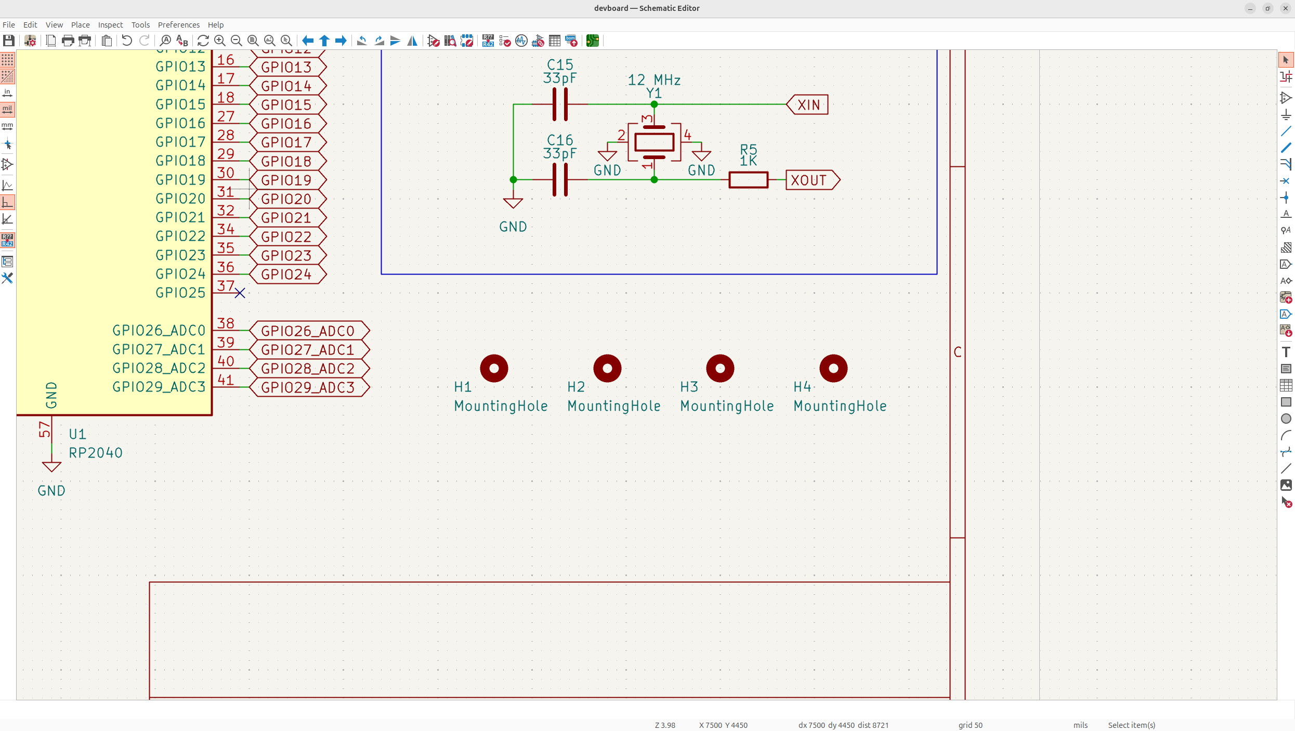
journal/Pasted image 20250928215223.png
