KaiPereira/build-a-devboard/journal/Pasted image 20250928215313.png

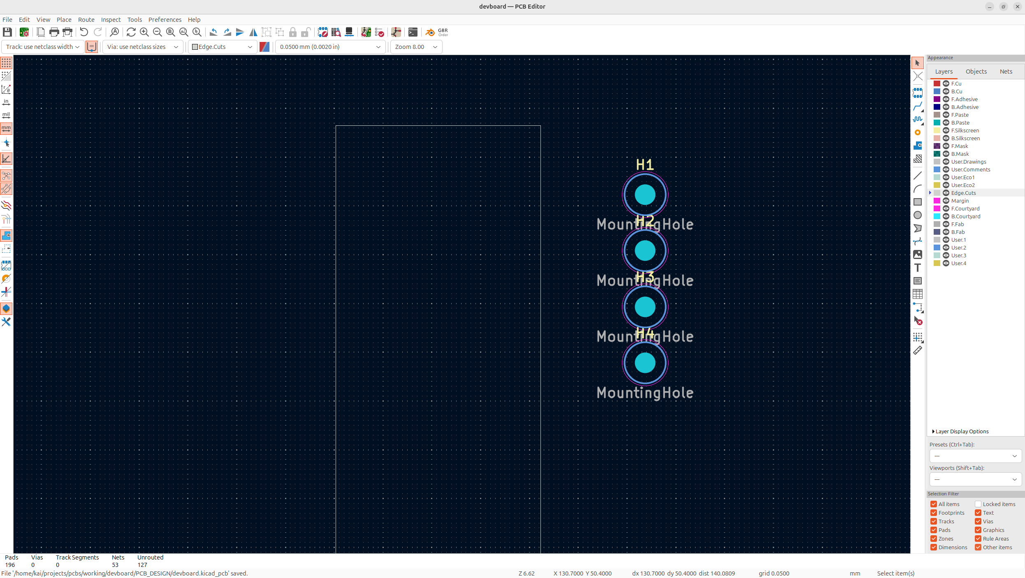
journal/Pasted image 20250928215313.png
