KaiPereira/build-a-devboard/journal/Pasted image 20250928215828.png

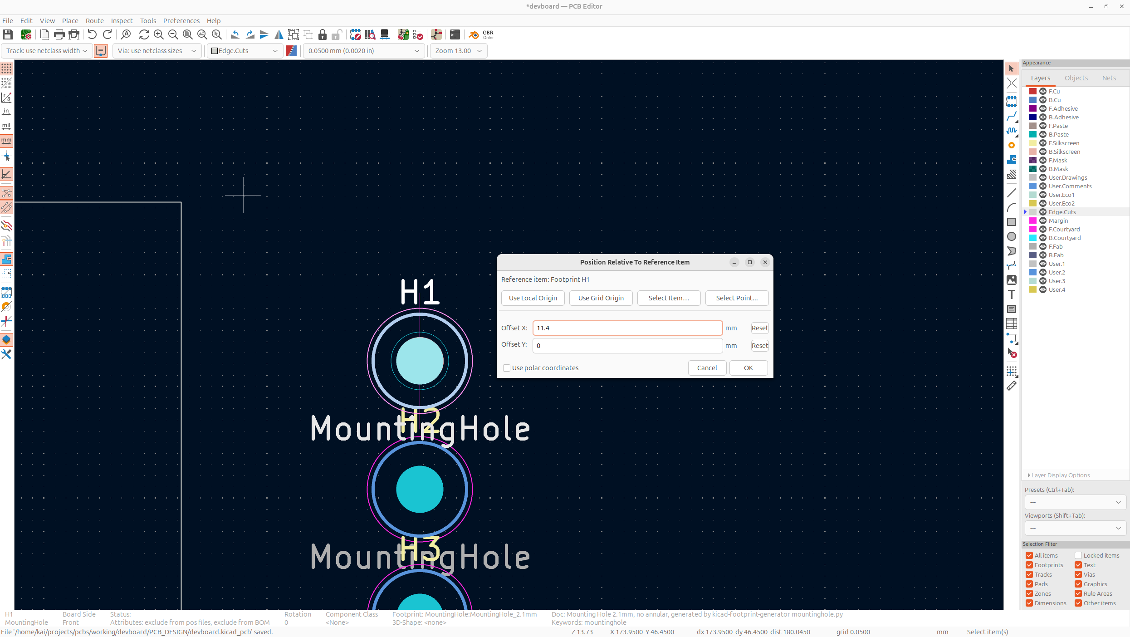
journal/Pasted image 20250928215828.png
