KaiPereira/build-a-devboard/journal/Pasted image 20250928220018.png

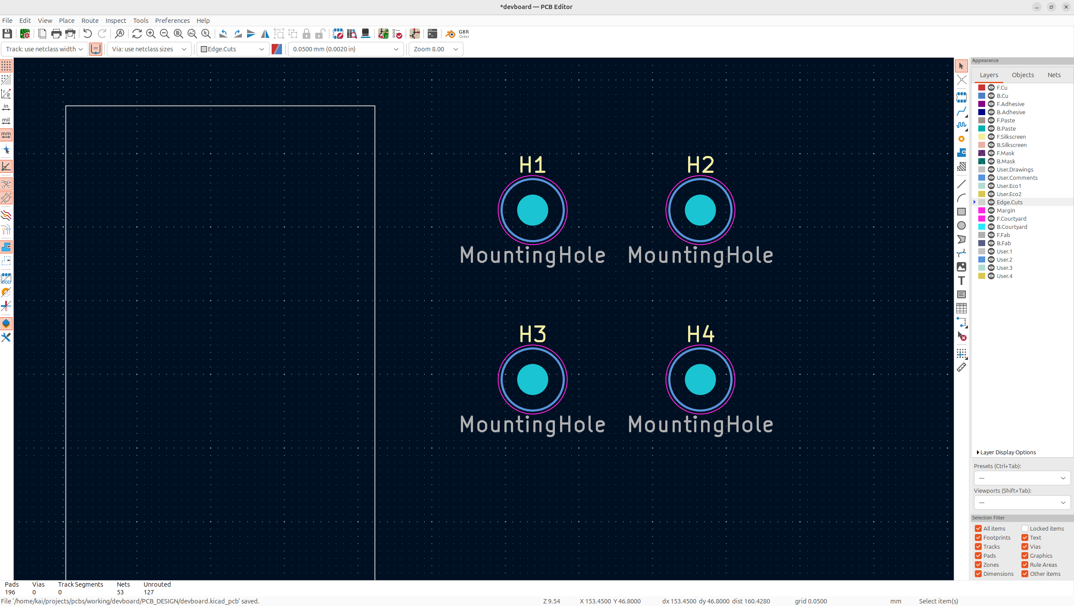
journal/Pasted image 20250928220018.png
