KaiPereira/build-a-devboard/journal/Pasted image 20250929114251.png

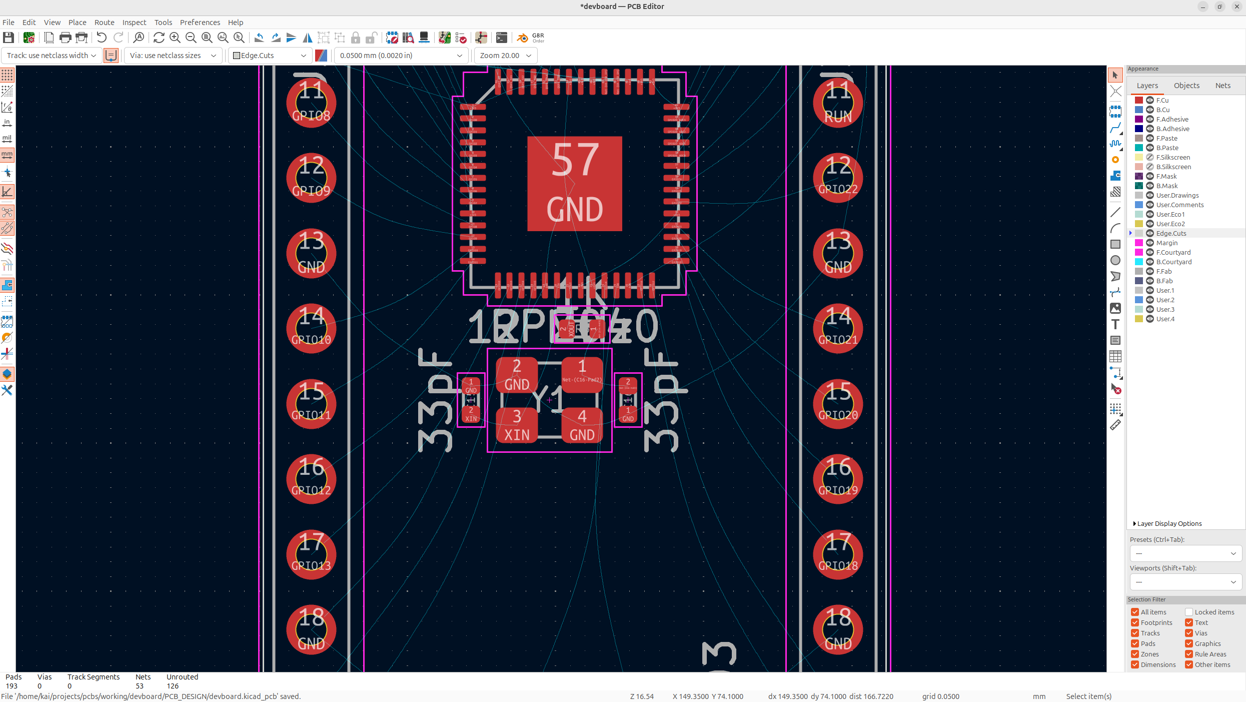
journal/Pasted image 20250929114251.png
