KaiPereira/build-a-devboard/journal/Pasted image 20250929133900.png

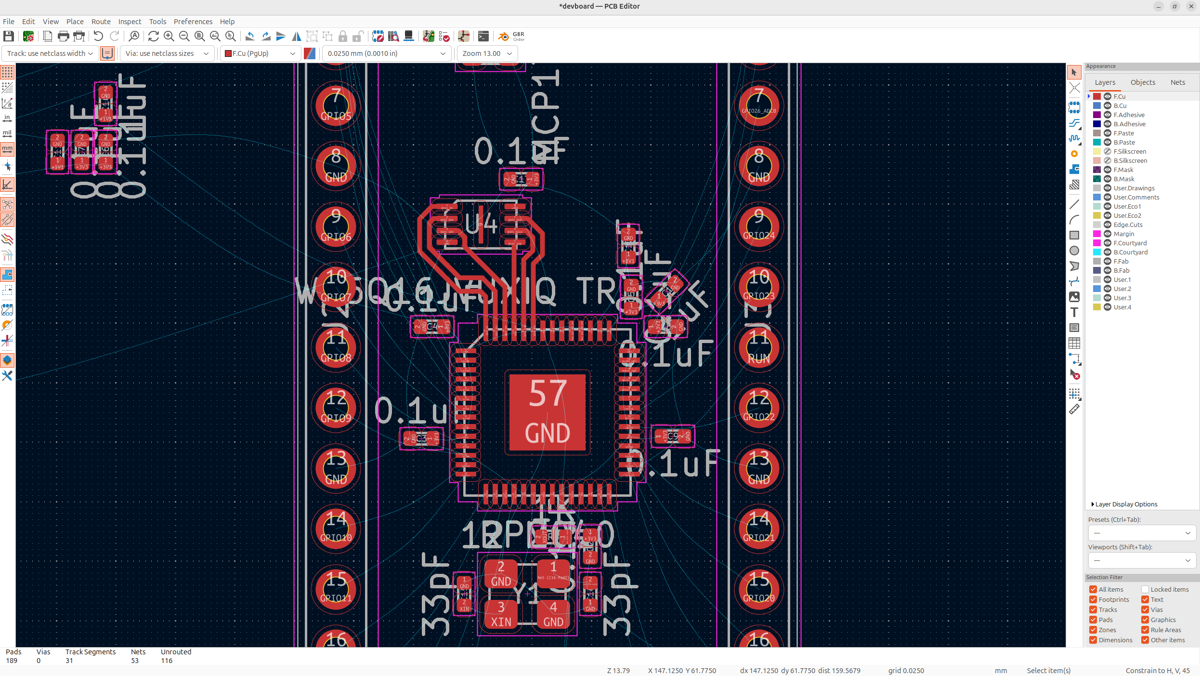
journal/Pasted image 20250929133900.png
