KaiPereira/build-a-devboard/journal/Pasted image 20250929135204.png

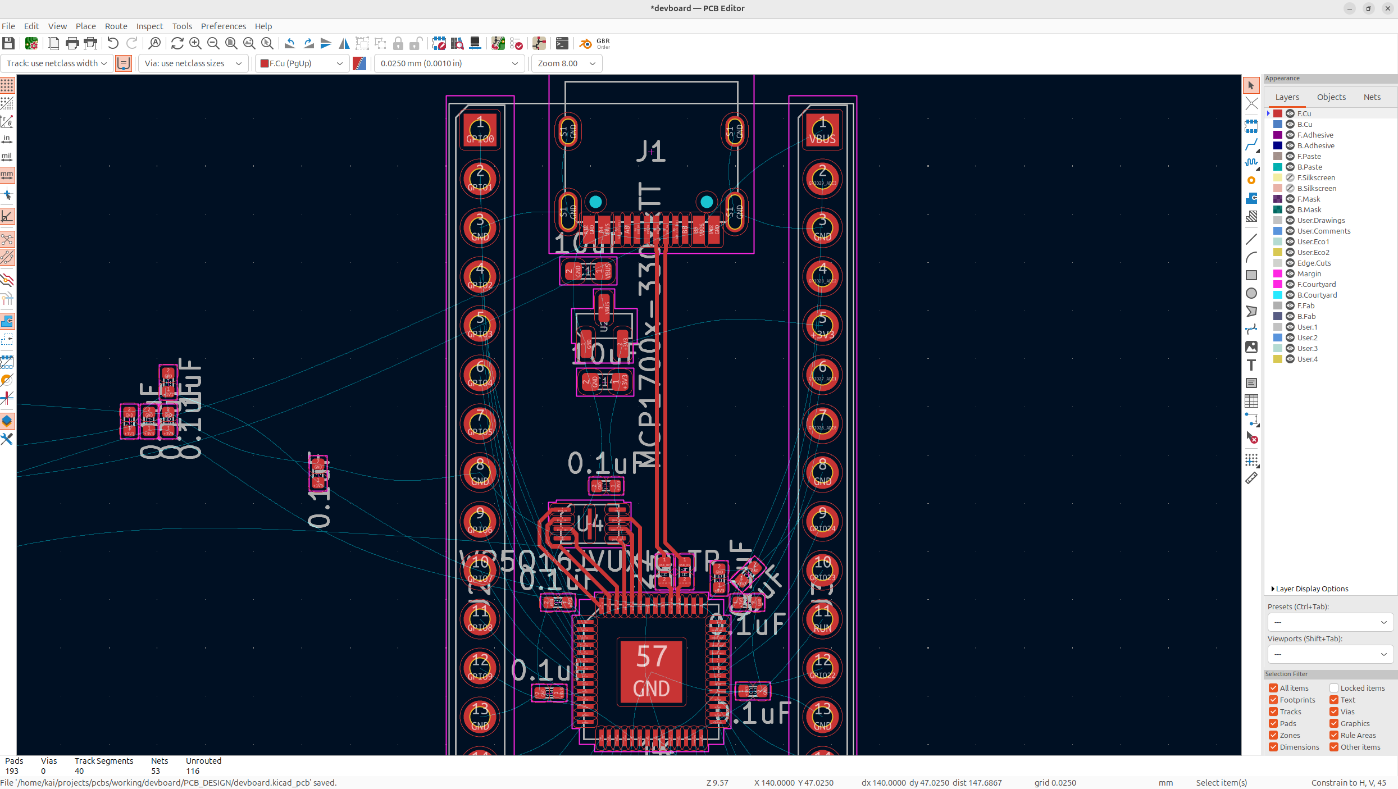
journal/Pasted image 20250929135204.png
