KaiPereira/build-a-devboard/journal/Pasted image 20250929135324.png

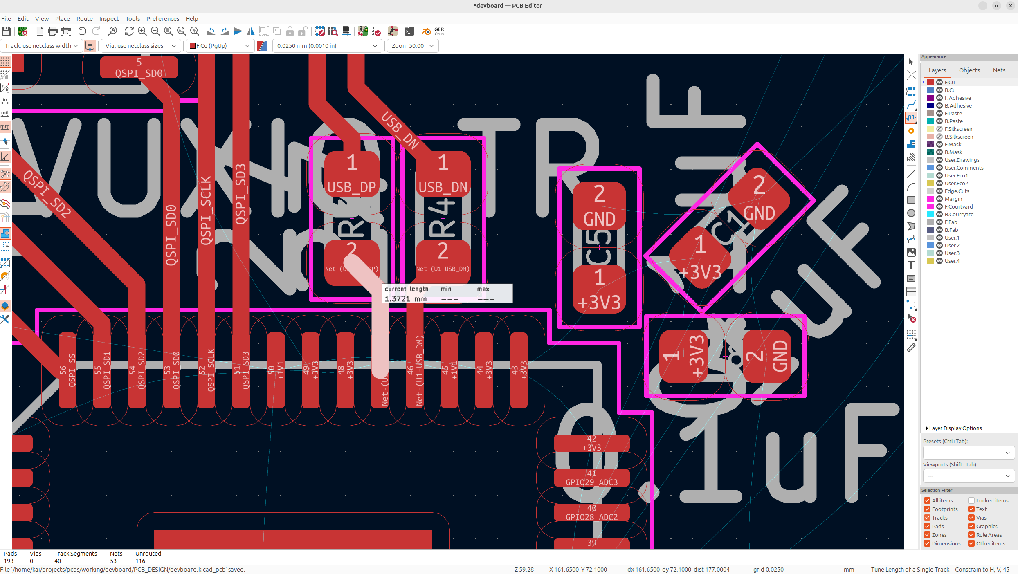
journal/Pasted image 20250929135324.png
