KaiPereira/build-a-devboard/journal/Pasted image 20250929135538.png

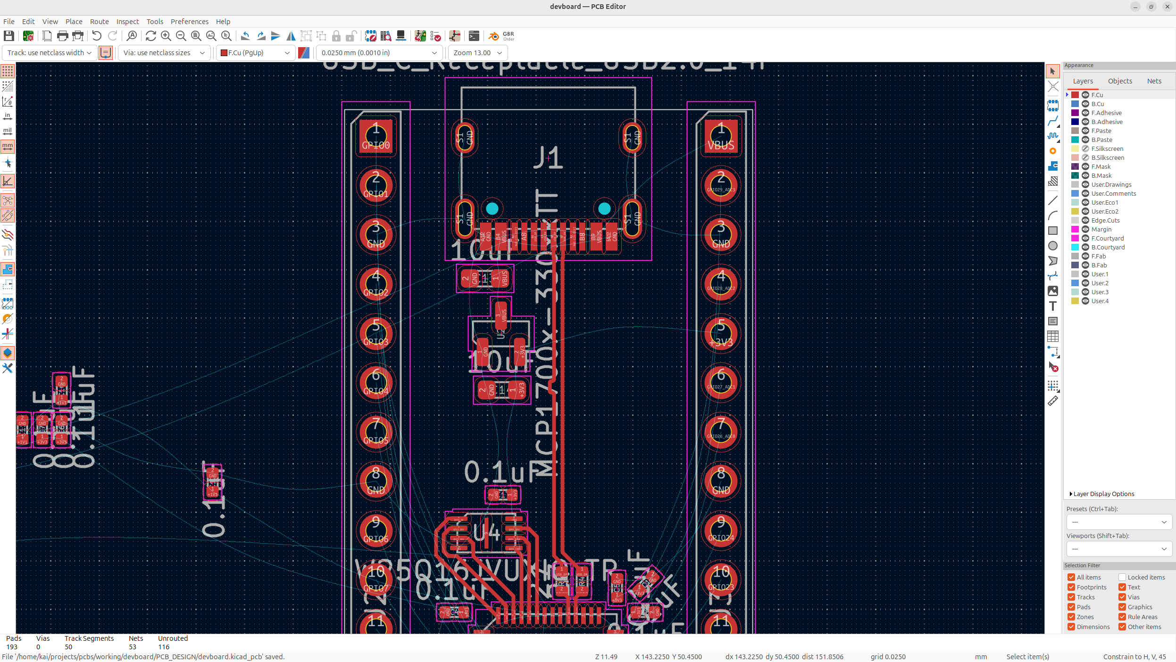
journal/Pasted image 20250929135538.png
