KaiPereira/build-a-devboard/journal/Pasted image 20250929155114.png

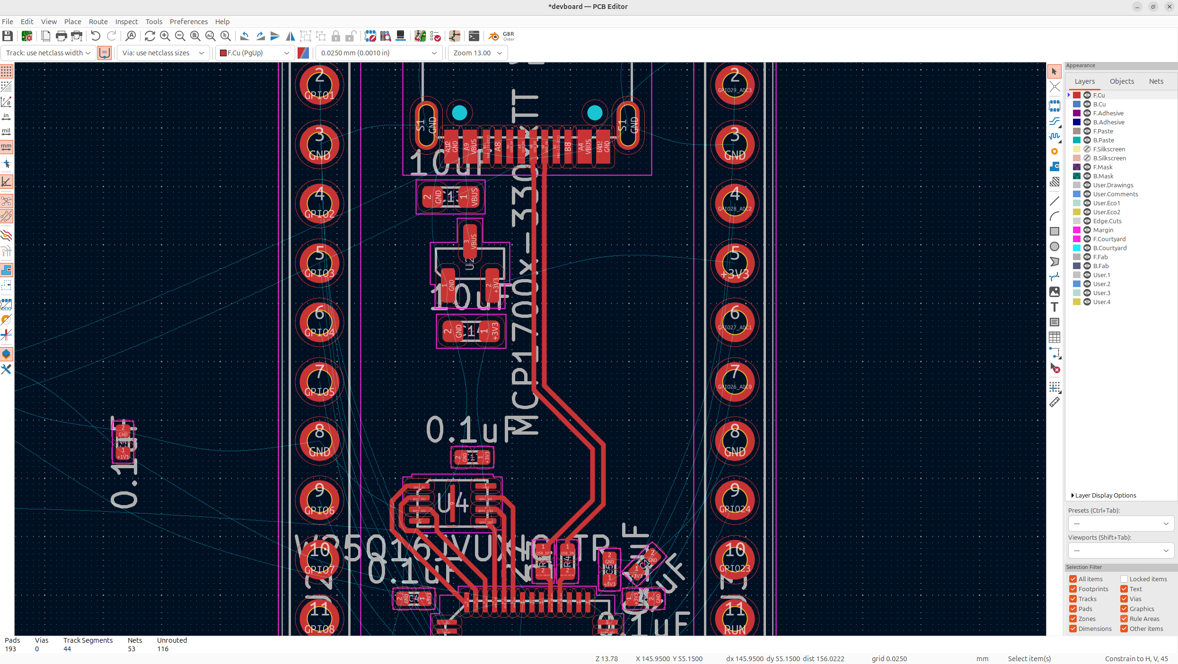
journal/Pasted image 20250929155114.png
