KaiPereira/build-a-devboard/journal/Pasted image 20250929155310.png

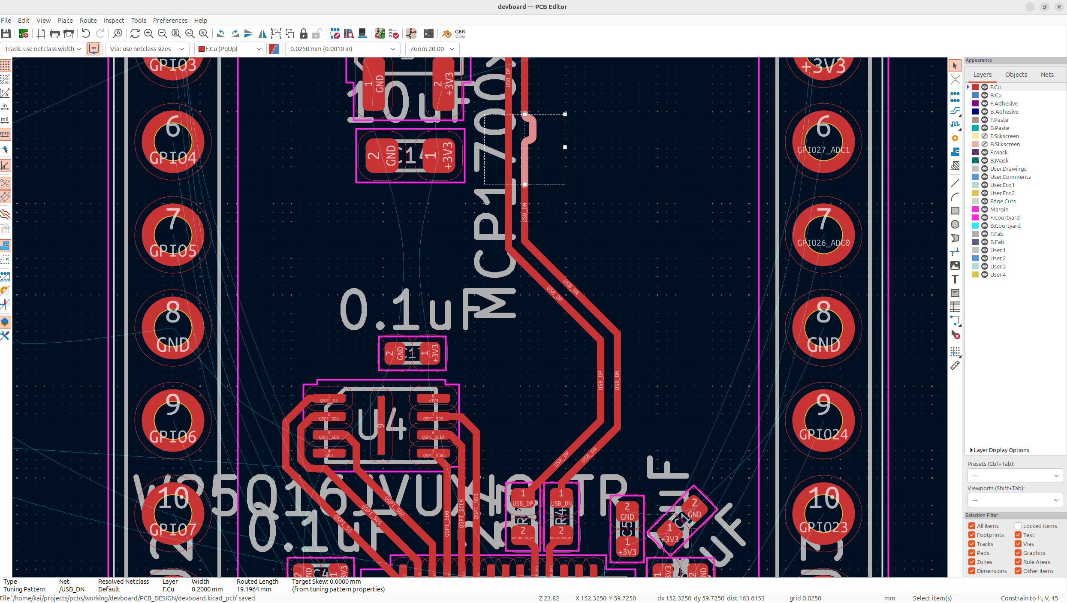
journal/Pasted image 20250929155310.png
