KaiPereira/build-a-devboard/journal/Pasted image 20250929163202.png

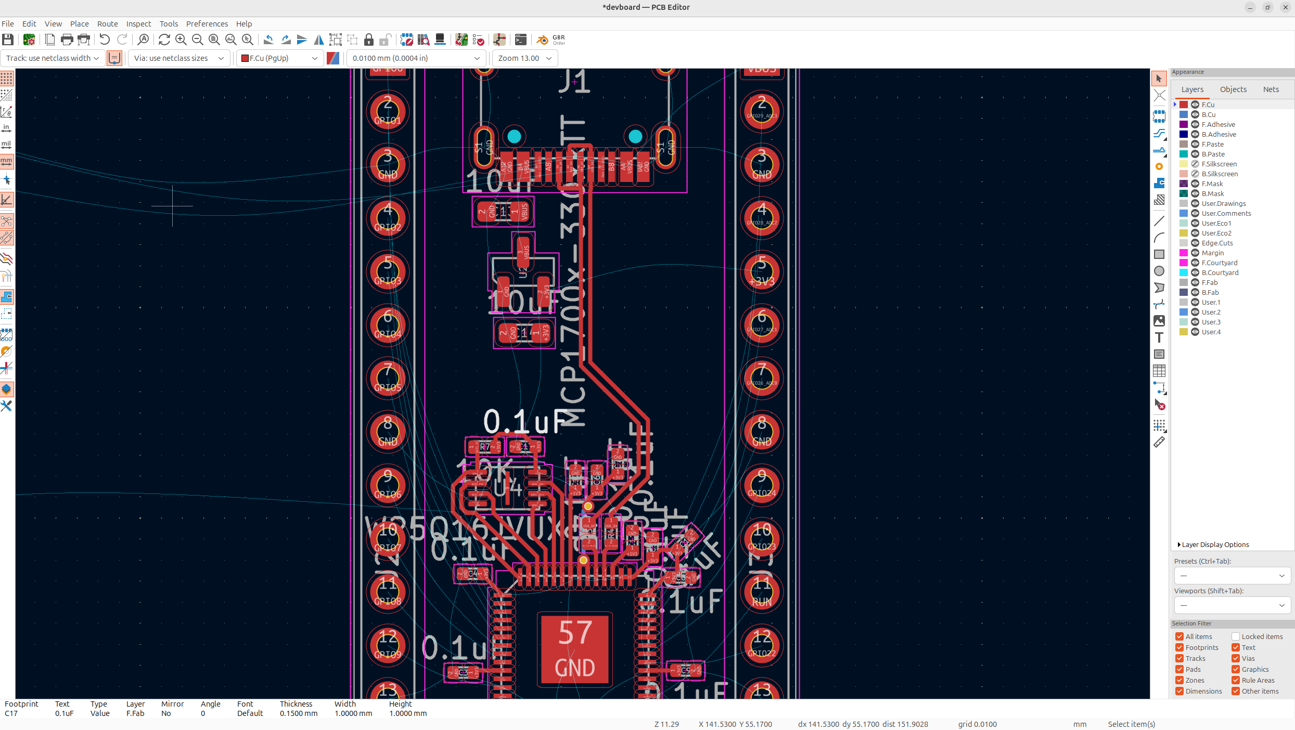
journal/Pasted image 20250929163202.png
