KaiPereira/build-a-devboard/journal/Pasted image 20250929221056.png

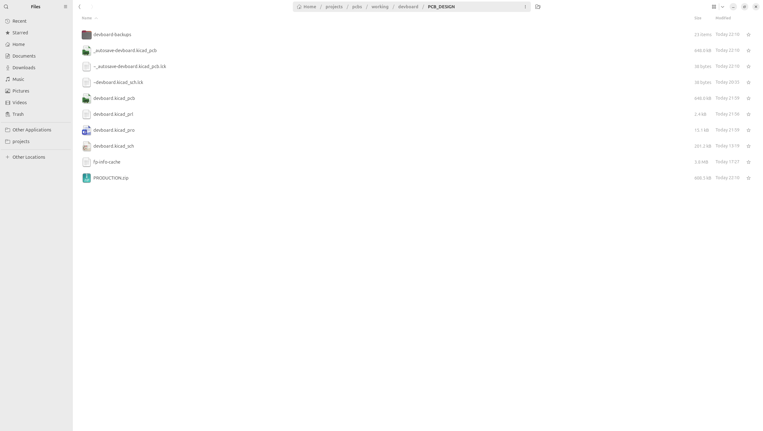
journal/Pasted image 20250929221056.png
