KaiPereira/build-a-devboard/journal/Pasted image 20250929221142.png

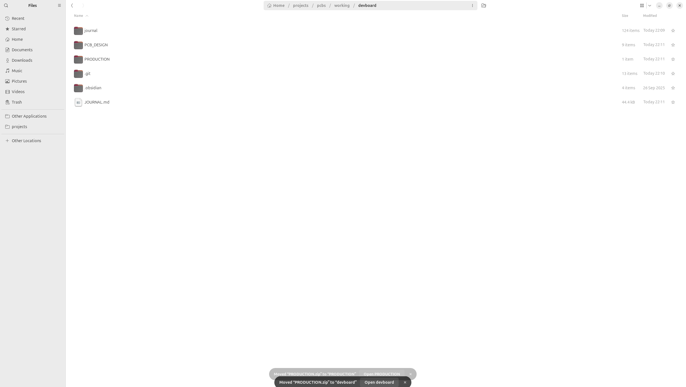
journal/Pasted image 20250929221142.png
