KaiPereira/build-a-devboard/journal/Pasted image 20250930151400.png

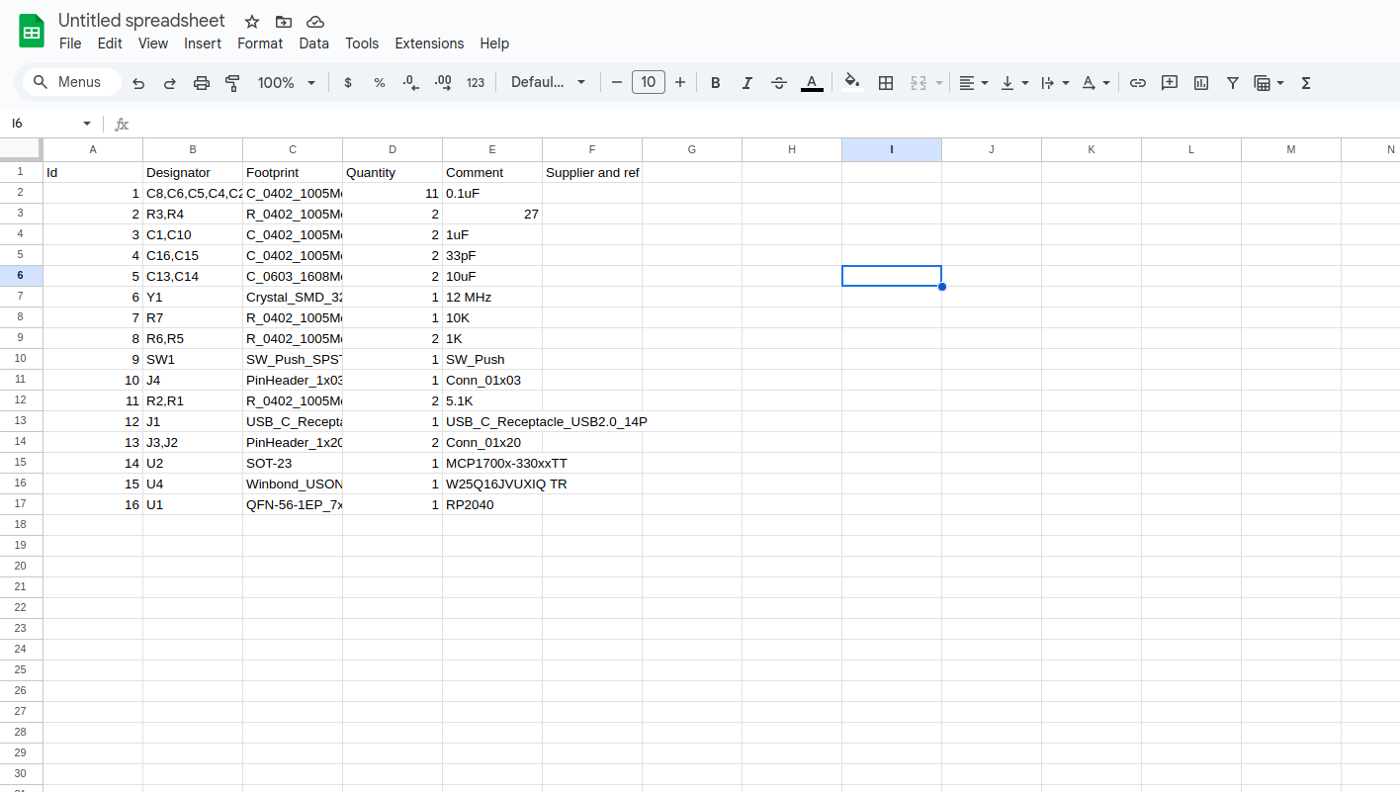
journal/Pasted image 20250930151400.png
