KaiPereira/build-a-devboard/journal/Pasted image 20250930153449.png

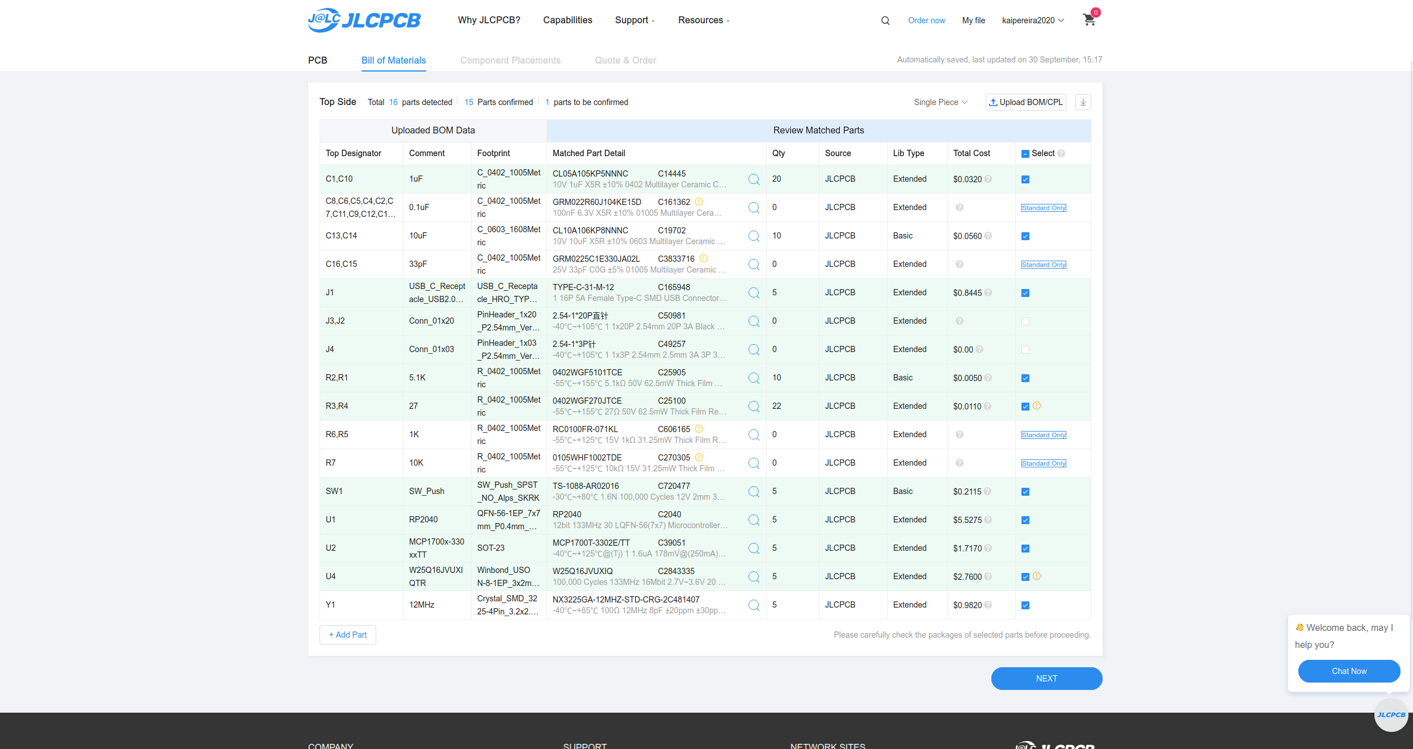
journal/Pasted image 20250930153449.png
