KaiPereira/build-a-devboard/journal/Pasted image 20250930155054.png

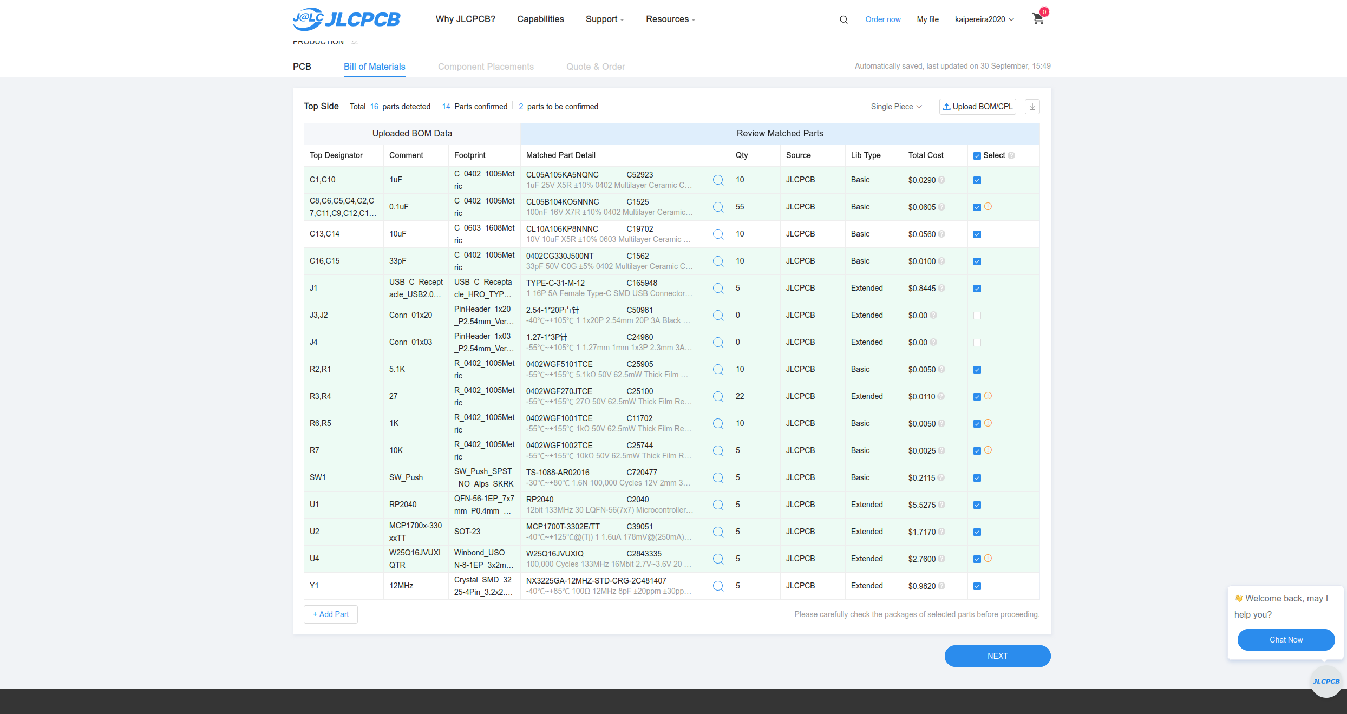
journal/Pasted image 20250930155054.png
